MichalVarsanyi/VoxLink/Firmware/Vivado/Projects/VoxLink_Controller/VoxLink_Controller.runs/fifo_generator_0_synth_1/.vivado.begin.rst

<?xml version="1.0"?>
<ProcessHandle Version="1" Minor="0">
    <Process Command="vivado.bat" Owner="varsa" Host="LAPTOP-GK6ER3TV" Pid="4304" HostCore="22" HostMemory="033736019968">
    </Process>
</ProcessHandle>
