MichalVarsanyi/VoxLink/Hardware/Controller_Board/images/fb_res1.png

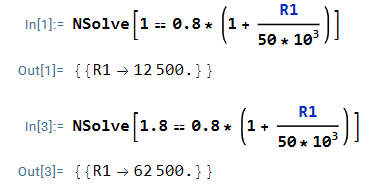
Hardware/Controller_Board/images/fb_res1.png
