MichalVarsanyi/VoxLink/Hardware/Controller_Board/images/hub_cfg.png

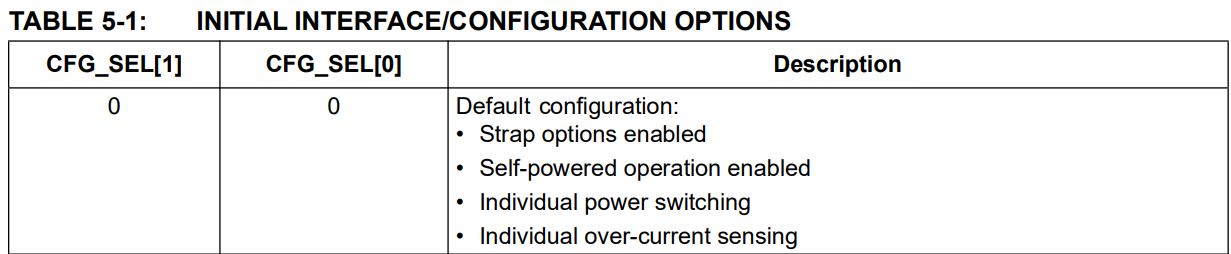
Hardware/Controller_Board/images/hub_cfg.png
