MichalVarsanyi/VoxLink/Hardware/Controller_Board/images/power_estimation.png

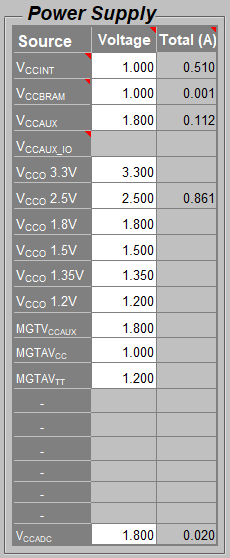
Hardware/Controller_Board/images/power_estimation.png
