MichalVarsanyi/VoxLink/Hardware/Programmer_Shell_Module/images/scheme_vox.png

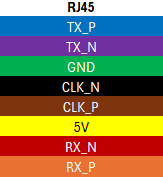
Hardware/Programmer_Shell_Module/images/scheme_vox.png
