MichalVarsanyi/VoxLink/Hardware/Sensor_Board/images/banana.bmp

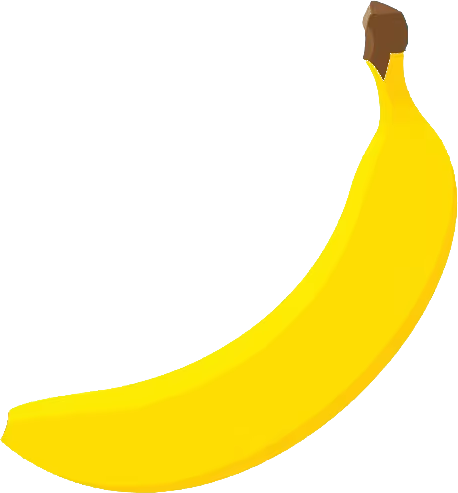
Hardware/Sensor_Board/images/banana.bmp
