MichalVarsanyi/VoxLink/Hardware/Sensor_Board/images/banana_flipped.bmp

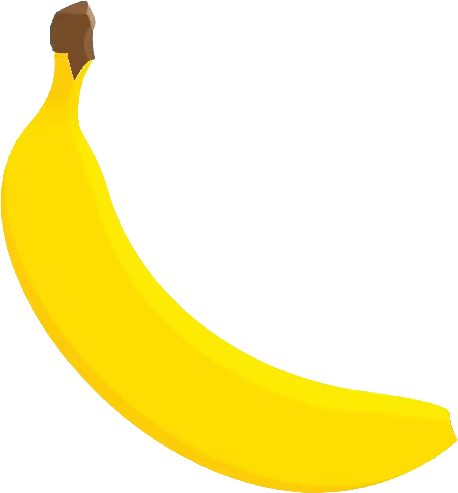
Hardware/Sensor_Board/images/banana_flipped.bmp
