MichalVarsanyi/VoxLink/Hardware/Sensor_Board/images/bno086_ps01.png

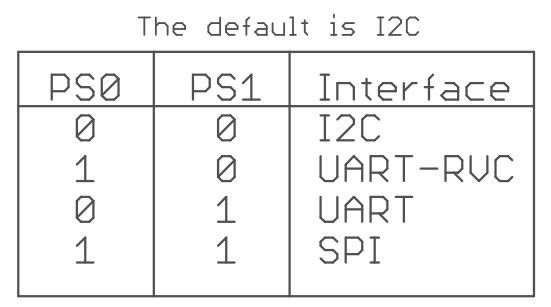
Hardware/Sensor_Board/images/bno086_ps01.png
