MichalVarsanyi/VoxLink/Hardware/Sensor_Board/images/datasheet_filtering.png

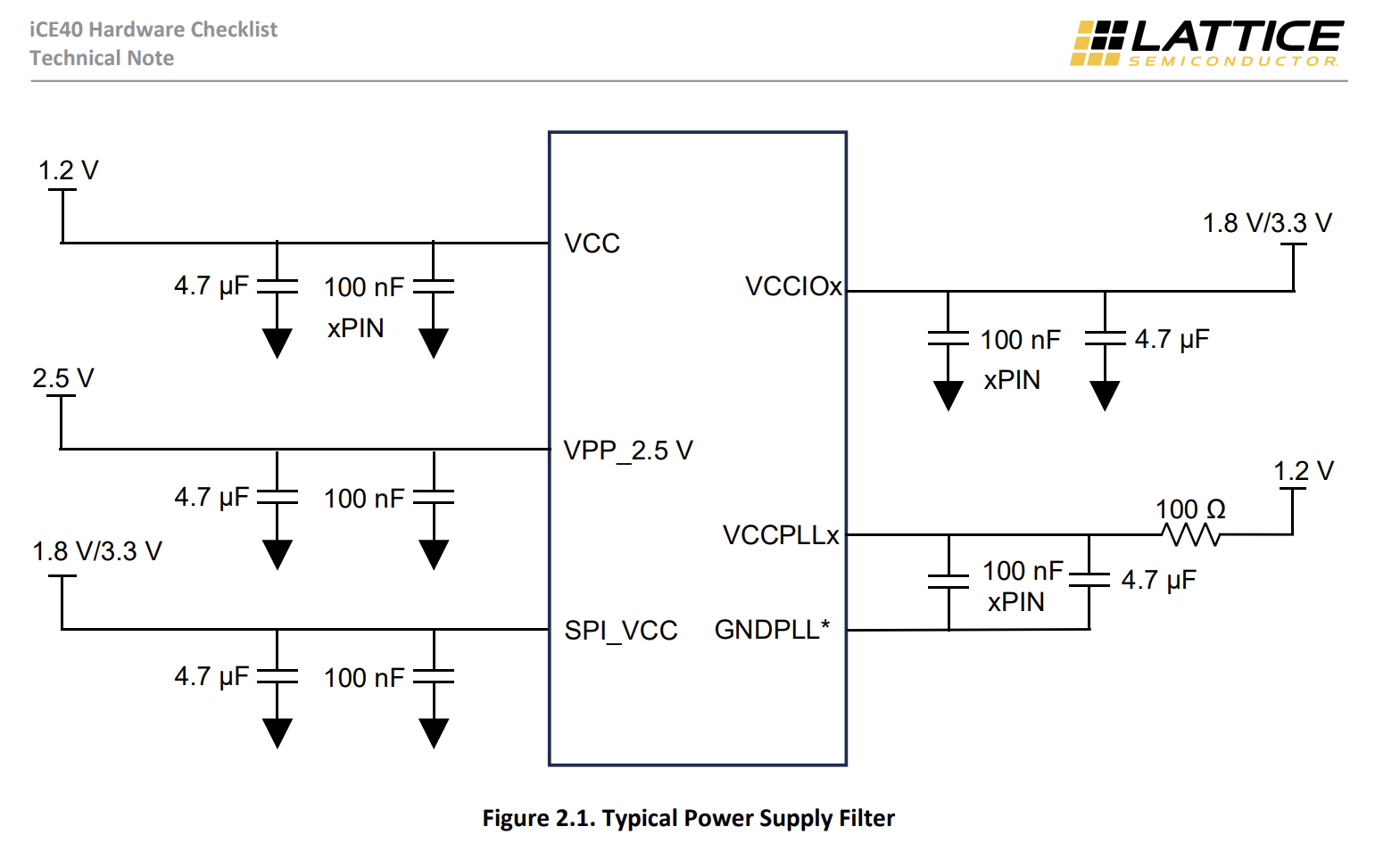
Hardware/Sensor_Board/images/datasheet_filtering.png
