MichalVarsanyi/VoxLink/Hardware/Sensor_Board/images/ilim.png

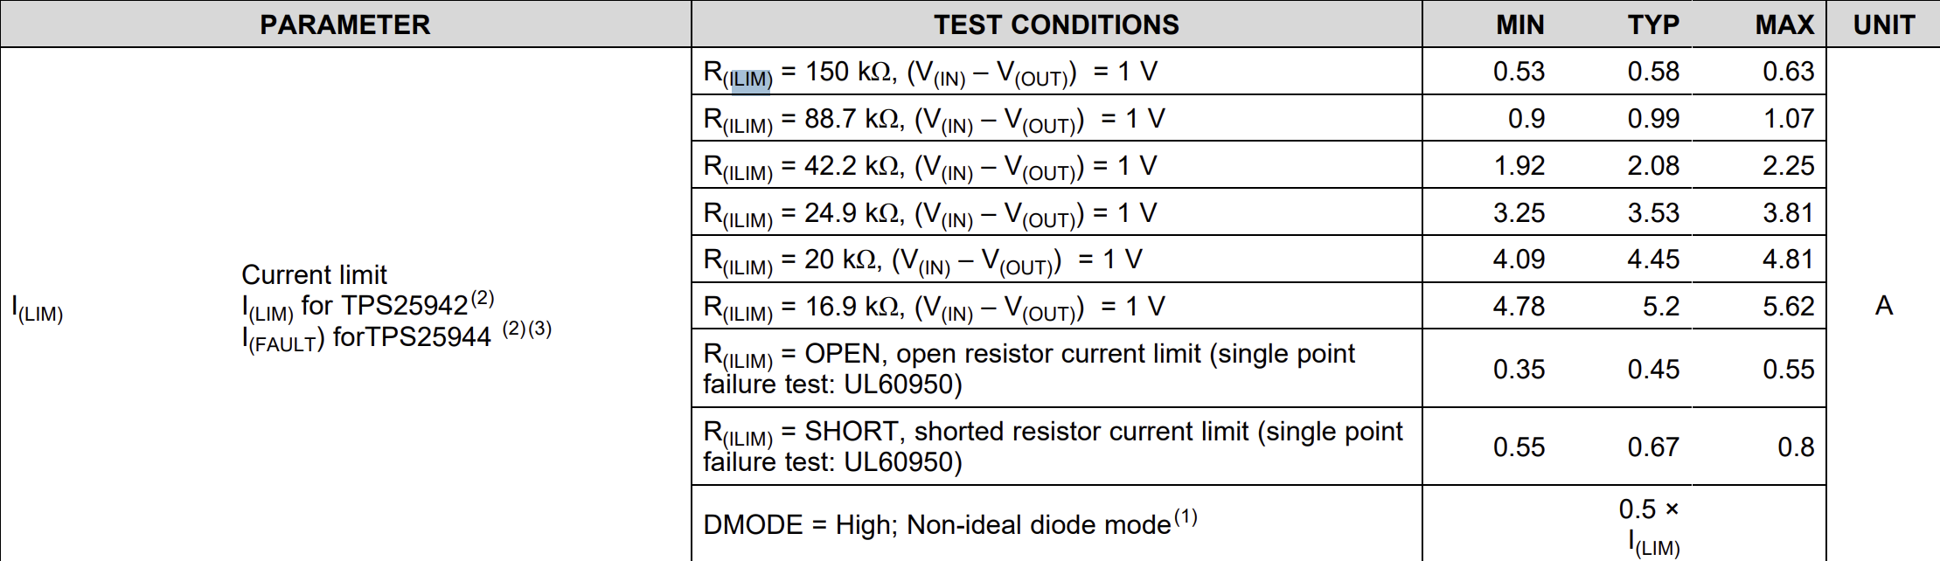
Hardware/Sensor_Board/images/ilim.png
