MichalVarsanyi/VoxLink/images/VoxLink_Block_Diagram_Simplified_Ethernet.jpg

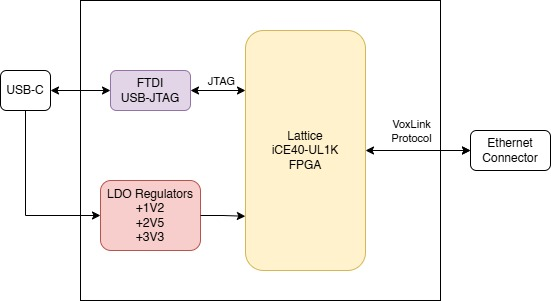
images/VoxLink_Block_Diagram_Simplified_Ethernet.jpg
