MichalVarsanyi/VoxLink/Hardware/Sensor_Board/images/ethernet_wiring.jpg

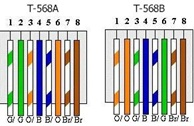
Hardware/Sensor_Board/images/ethernet_wiring.jpg
