MichalVarsanyi/VoxLink/Firmware/Lattice/Source/Verilog/Top_VoxLink_Protocol.v

//////////////////////////////////////////////////////////////////////////////////
// Company: Czech Technical University in Prague
// Engineer: Michal Varsanyi
// 
// Create Date: 26/DEC/2025
// Design Name: Top_VoxLink_Protocol
// Module Name: Top
// Project Name: VoxLink_Protocol
// Target Devices: VoxLink Sensor Board - iCE40UL1K-CM36AI
// Tool Versions: 
// Description: 
// 
// Dependencies: 
// 
// Revision: 1.0
// Revision 0.01 - File Created
// Additional Comments:
// 
//////////////////////////////////////////////////////////////////////////////////

module Top(
    // Clock
    input       clk_12mhz, 

    // Sensor
    inout       i2c_scl,
    inout       i2c_sda,
    output      bno_rstn,
    input       bno_interrupt,

    // LEDs
    output      led_io,

    // VoxLink
    input       vox_in_clk_p,
    input       vox_in_clk_n,

    output      vox_out_clk_p,
    output      vox_out_clk_n,

    input       vox_in_rxd_p,
    input       vox_in_rxd_n,

    output      vox_out_rxd_p,
    output      vox_out_rxd_n
);

//--------------------------------------------------------------------------------------------- //       
//  Wire Declarations
//--------------------------------------------------------------------------------------------- //

    localparam SYSTEM_CLOCK     = 84_000_000;
    localparam VOX_FREQUENCY    = 21_000_000;
    localparam I2C_FREQUENCY    = 400_000;

    // Clock and Reset
    wire            sys_clk;        // 100.5 MHz
    wire            sys_clkout;
    wire            sys_rst;
    wire            locked;
    assign          sys_rst = !locked;

    // VoxLink CDC outputs
    wire            vox_clk_sync;
    wire            vox_rxd_sync;

    // LED
    reg             led_io_r;
    reg             nack_sticky_r;


    //----------------EMI Improvements----------------//
    // Connect the _N to GND to facilitate low impedance return path
    assign vox_in_clk_n     = 1'b0;
    assign vox_out_clk_n    = 1'b0;
    assign vox_in_rxd_n     = 1'b0;
    assign vox_out_rxd_n    = 1'b0;

    // Assign the BNO RSTN pin to a deterministic value
    assign bno_rstn         = ~sys_rst;


//--------------------------------------------------------------------------------------------- //       
//  Clock
//--------------------------------------------------------------------------------------------- //

    // BUFG rounting of external clock
    wire clk_12mhz_bufg;

    // Routing inside the GBUF clock fabric
    SB_GB clk_in (
        .USER_SIGNAL_TO_GLOBAL_BUFFER(clk_12mhz),
        .GLOBAL_BUFFER_OUTPUT(clk_12mhz_bufg)
    );

    SB_PLL40_CORE #(
        .FEEDBACK_PATH("SIMPLE"),
        .DIVR(0),
        .DIVF(55),                  // VCO = 12 * 56 = 672 MHz
        .DIVQ(3),                   // F_out = 672 / 8 = 84 MHz
        .FILTER_RANGE(1)
    ) u_pll (
        .REFERENCECLK(clk_12mhz_bufg),
        .PLLOUTCORE(sys_clkout),
        .LOCK(locked),
        .EXTFEEDBACK(),
        .DYNAMICDELAY(),
        .RESETB(1'b1),              // Keep PLL enabled
        .BYPASS(1'b0)               // No bypass
    );

    SB_GB clk_pll (
        .USER_SIGNAL_TO_GLOBAL_BUFFER(sys_clkout),
        .GLOBAL_BUFFER_OUTPUT(sys_clk)
    );

//--------------------------------------------------------------------------------------------- //       
//  Cross Domain Crossing
//--------------------------------------------------------------------------------------------- //

    // VoxLink CLK Input
    wire vox_clk_ff1;
    wire vox_clk_ff2;

    SB_DFF vox_clk_cdc_stage_1 (
        .Q(vox_clk_ff1),
        .C(sys_clk),
        .D(vox_in_clk_p)
    );

    SB_DFF vox_clk_cdc_stage_2 (
        .Q(vox_clk_ff2),
        .C(sys_clk),
        .D(vox_clk_ff1)
    );

    assign vox_clk_sync = vox_clk_ff2;



    // VoxLink RXD Input
    wire vox_rxd_ff1;
    wire vox_rxd_ff2;

    SB_DFF vox_rxd_cdc_stage_1 (
        .Q(vox_rxd_ff1),
        .C(sys_clk),
        .D(vox_in_rxd_p)
    );

    SB_DFF vox_rxd_cdc_stage_2 (
        .Q(vox_rxd_ff2),
        .C(sys_clk),
        .D(vox_rxd_ff1)
    );

    assign vox_rxd_sync = vox_rxd_ff2;



    // Sensor Interrupt
    wire bno_interrupt_ff1;
    wire bno_interrupt_ff2;

    SB_DFF bno_interrupt_cdc_stage_1 (
        .Q(bno_interrupt_ff1),
        .C(sys_clk),
        .D(bno_interrupt)
    );

    SB_DFF bno_interrupt_cdc_stage_2 (
        .Q(bno_interrupt_ff2),
        .C(sys_clk),
        .D(bno_interrupt_ff1)
    );

    assign bno_interrupt_sync = bno_interrupt_ff2;


//--------------------------------------------------------------------------------------------- //
// VoxLink Multinode Protocol
//--------------------------------------------------------------------------------------------- //

    wire [9:0]      node_addr_r;
    wire            fifo_overflow_sticky;

    VoxLink_Multinode_Protocol #(
        .CLK_FREQ(SYSTEM_CLOCK),
        .VOX_FREQ(VOX_FREQUENCY)
    ) VoxLink_Multinode_Protocol_Inst (
        // General
        .sys_clk        (sys_clk),
        .sys_rst        (sys_rst),

        // Data
        .vox_transmit_packet(packet_data_latched),

        // VoxLink
        .vox_in_clk_p   (vox_clk_sync),
        .vox_in_rxd_p   (vox_rxd_sync),

        .vox_out_rxd_p  (vox_out_rxd_p),
        .vox_out_clk_p  (vox_out_clk_p),

        // Node
        .node_addr_r(node_addr_r),

        // Diagnostics
        .fifo_overflow_sticky(fifo_overflow_sticky)
    );

//--------------------------------------------------------------------------------------------- //
//  NACK Sticky Flag
//--------------------------------------------------------------------------------------------- //

    always @(posedge sys_clk or posedge sys_rst)
    begin
        if (sys_rst)
            nack_sticky_r <= 1'b0;
        else if (target_nack)
            nack_sticky_r <= 1'b1;
    end

//--------------------------------------------------------------------------------------------- //
//  RGB Infrastructure
//--------------------------------------------------------------------------------------------- //

    SB_RGBA_DRV #(
        .CURRENT_MODE("0b1"),
        .RGB0_CURRENT("0b000001"),
        .RGB1_CURRENT(),
        .RGB2_CURRENT()
    ) led_driver (
        .CURREN(1'b1),
        .RGBLEDEN(1'b1),

        .RGB0PWM(nack_sticky_r),
        .RGB1PWM(),
        .RGB2PWM(),

        .RGB0(led_io),
        .RGB1(),
        .RGB2()
    );

//--------------------------------------------------------------------------------------------- // 
// Blinky LED
//--------------------------------------------------------------------------------------------- // 

    // reg [26:0]  blink_counter;

    // always @(posedge sys_clk or posedge sys_rst)
    // begin
    //     if(sys_rst)
    //     begin
    //         led_io_r        <= 1'b1;
    //     end
    //     else
    //     begin
    //         if(blink_counter == {27{1'b1}})
    //         begin
    //             blink_counter   <= {27{1'b0}};
    //             led_io_r        <= ~led_io_r;
    //         end
    //         else
    //         begin
    //             blink_counter   <= blink_counter + 1;
    //         end
    //     end
    // end


//--------------------------------------------------------------------------------------------- // 
// I2C Driver
//--------------------------------------------------------------------------------------------- // 

    wire [7:0] tx_data;
    wire       trigger_tx;
    wire       tx_done;
    wire       target_nack;

    wire [7:0] rx_data;
    wire       trigger_rx;
    wire       rx_valid;

    wire       finish_transaction;
    wire       driver_waiting;
    wire       driver_finished_tranaction;

    VoxLink_I2C_Driver #(
        .CLK_FREQ(SYSTEM_CLOCK),  // System Clock Frequency
        .I2C_FREQ(I2C_FREQUENCY)        // Target I2C Speed
    ) VoxLink_I2C_Driver_inst (
        // General
        .sys_clk        (sys_clk),
        .sys_rst        (sys_rst),

        // I2C Interface
        .i2c_scl        (i2c_scl),
        .i2c_sda        (i2c_sda),

        // Control Signals
        .tx_data(tx_data),                          // Data to send
        .trigger_tx(trigger_tx),                    // Pulse HIGH to write the tx_data byte
        .tx_done(tx_done),                          // Pulses HIGH when writing the byte is complete
        .target_nack(target_nack),                  // HIGH = The sensor ignored us! (Did not ACK our write) Blasphemy!

        .rx_data(rx_data),                          // Data received
        .trigger_rx(trigger_rx),                    // Pulse HIGH to trigger a read operation
        .rx_valid(rx_valid),                        // Pulses HIGH when rx_data is valid

        .finish_transaction(finish_transaction),    // Set HIGH before the ACK of the last byte we want to receive + signal triggers the STOP sequence
        .driver_waiting(driver_waiting),            // Driver is waiting for command
        .driver_finished_tranaction(driver_finished_tranaction)     // Driver has finished a sequence of transaction commands and is now in the idle state
    );

//--------------------------------------------------------------------------------------------- // 
// BNO086 Sensor Driver
//--------------------------------------------------------------------------------------------- // 

    wire [79:0] sensor_data;
    wire        sensor_data_ready;

    VoxLink_BNO_Driver #(
        .BNO_ADDRESS(7'h4B)                         // Check the SA0 pin of the BNO086 in the schematic diagram
    ) VoxLink_BNO_Driver_Inst (
        // General
        .sys_clk(sys_clk),
        .sys_rst(sys_rst),
        
        // Control Signals
        .tx_data(tx_data),                          // Data to send
        .trigger_tx(trigger_tx),                    // Pulse HIGH to write the tx_data byte
        .tx_done(tx_done),                          // Pulses HIGH when writing the byte is complete
        .target_nack(target_nack),                  // HIGH = The sensor ignored us! (Did not ACK our write) Blasphemy!

        .rx_data(rx_data),                          // Data received
        .trigger_rx(trigger_rx),                    // Pulse HIGH to trigger a read operation
        .rx_valid(rx_valid),                        // Pulses HIGH when rx_data is valid

        .finish_transaction(finish_transaction),    // Set HIGH before the ACK of the last byte we want to receive + signal triggers the STOP sequence
        .driver_waiting(driver_waiting),            // Driver is waiting for command
        .driver_finished_tranaction(driver_finished_tranaction),    // Driver has finished a sequence of transaction commands and is now in the idle state

        // Sensor
        .bno_interrupt(bno_interrupt_sync),              // Interrupt from the BNO sensor

        .sensor_data(sensor_data),                  // Latched data from the sensor
        .sensor_data_ready(sensor_data_ready)
    );

//--------------------------------------------------------------------------------------------- // 
// VoxLink Packet Builder
//--------------------------------------------------------------------------------------------- // 

    wire [111:0] packet_data;
    wire         packet_ready;

    reg [111:0] packet_data_latched;

    assign vox_transmit_packet = packet_data_latched;

    always @(posedge sys_clk or posedge sys_rst)
    begin
        if (sys_rst)
        begin
            packet_data_latched <= 112'd0;
        end
        else if (packet_ready && node_addr_r != 10'd0)
        begin
            packet_data_latched <= packet_data;
        end
    end

    VoxLink_Packet_Builder #(
        .COMMAND(6'h03),
        .CLK_FREQ_HZ(SYSTEM_CLOCK)
    ) VoxLink_Packet_Builder_Inst (
        // General
        .sys_clk(sys_clk),
        .sys_rst(sys_rst),

        // Sensor Data
        .sensor_data(sensor_data),
        .sensor_data_ready(sensor_data_ready),

        // Node Info
        .address(node_addr_r),

        // Output Packet
        .packet_data(packet_data),
        .packet_ready(packet_ready)
    );
endmodule
