MichalVarsanyi/VoxLink/Firmware/Vivado/Projects/VoxLink_Controller/VoxLink_Controller.srcs/sources_1/new/VoxLink_BRAM_Storage.v

`timescale 1ns / 1ps

module VoxLink_BRAM_Storage (
    input           sys_clk,

    input  [111:0]  rx_packet,
    input           rx_valid,

    input  [6:0]    node_select,
    output [111:0]  node_packet
);

    wire [6:0]      bram_addr = rx_valid ? rx_packet[108:102] : node_select;
    wire [111:0]    bram_dout;

    blk_mem_gen_0 u_bram (
        .clka  (sys_clk),
        .ena   (1'b1),
        .wea   (rx_valid),
        .addra (bram_addr),
        .dina  (rx_packet),
        .douta (bram_dout)
    );

    assign node_packet = bram_dout;

endmodule
