MichalVarsanyi/VoxLink/Firmware/Vivado/Projects/VoxLink_Controller/VoxLink_Controller.cache/ip/2024.1/a/6/a6a7915305ae47ab/blk_mem_gen_0_stub.v

// Copyright 1986-2022 Xilinx, Inc. All Rights Reserved.
// Copyright 2022-2024 Advanced Micro Devices, Inc. All Rights Reserved.
// --------------------------------------------------------------------------------
// Tool Version: Vivado v.2024.1 (win64) Build 5076996 Wed May 22 18:37:14 MDT 2024
// Date        : Tue May  5 16:36:00 2026
// Host        : LAPTOP-GK6ER3TV running 64-bit major release  (build 9200)
// Command     : write_verilog -force -mode synth_stub -rename_top decalper_eb_ot_sdeen_pot_pi_dehcac_xnilix -prefix
//               decalper_eb_ot_sdeen_pot_pi_dehcac_xnilix_ blk_mem_gen_0_stub.v
// Design      : blk_mem_gen_0
// Purpose     : Stub declaration of top-level module interface
// Device      : xc7a35tcsg324-1
// --------------------------------------------------------------------------------

// This empty module with port declaration file causes synthesis tools to infer a black box for IP.
// The synthesis directives are for Synopsys Synplify support to prevent IO buffer insertion.
// Please paste the declaration into a Verilog source file or add the file as an additional source.
(* x_core_info = "blk_mem_gen_v8_4_8,Vivado 2024.1" *)
module decalper_eb_ot_sdeen_pot_pi_dehcac_xnilix(clka, ena, wea, addra, dina, douta)
/* synthesis syn_black_box black_box_pad_pin="ena,wea[0:0],addra[6:0],dina[111:0],douta[111:0]" */
/* synthesis syn_force_seq_prim="clka" */;
  input clka /* synthesis syn_isclock = 1 */;
  input ena;
  input [0:0]wea;
  input [6:0]addra;
  input [111:0]dina;
  output [111:0]douta;
endmodule
