MichalVarsanyi/VoxLink/Firmware/Vivado/Projects/VoxLink_Controller/VoxLink_Controller.cache/ip/2024.1/6/f/6fbaab5b1b3133b9/u_ila_0_stub.v

// Copyright 1986-2022 Xilinx, Inc. All Rights Reserved.
// Copyright 2022-2024 Advanced Micro Devices, Inc. All Rights Reserved.
// --------------------------------------------------------------------------------
// Tool Version: Vivado v.2024.1 (win64) Build 5076996 Wed May 22 18:37:14 MDT 2024
// Date        : Thu Apr 30 17:34:39 2026
// Host        : LAPTOP-GK6ER3TV running 64-bit major release  (build 9200)
// Command     : write_verilog -force -mode synth_stub -rename_top decalper_eb_ot_sdeen_pot_pi_dehcac_xnilix -prefix
//               decalper_eb_ot_sdeen_pot_pi_dehcac_xnilix_ u_ila_0_stub.v
// Design      : u_ila_0
// Purpose     : Stub declaration of top-level module interface
// Device      : xc7a35tcsg324-1
// --------------------------------------------------------------------------------

// This empty module with port declaration file causes synthesis tools to infer a black box for IP.
// The synthesis directives are for Synopsys Synplify support to prevent IO buffer insertion.
// Please paste the declaration into a Verilog source file or add the file as an additional source.
(* X_CORE_INFO = "ila,Vivado 2024.1" *)
module decalper_eb_ot_sdeen_pot_pi_dehcac_xnilix(clk, probe0, probe1, probe2, probe3, probe4, probe5, 
  probe6, probe7, probe8, probe9, probe10, probe11, probe12, probe13)
/* synthesis syn_black_box black_box_pad_pin="probe0[13:0],probe1[2:0],probe2[14:0],probe3[7:0],probe4[31:0],probe5[14:0],probe6[39:0],probe7[1:0],probe8[111:0],probe9[14:0],probe10[7:0],probe11[63:0],probe12[0:0],probe13[0:0]" */
/* synthesis syn_force_seq_prim="clk" */;
  input clk /* synthesis syn_isclock = 1 */;
  input [13:0]probe0;
  input [2:0]probe1;
  input [14:0]probe2;
  input [7:0]probe3;
  input [31:0]probe4;
  input [14:0]probe5;
  input [39:0]probe6;
  input [1:0]probe7;
  input [111:0]probe8;
  input [14:0]probe9;
  input [7:0]probe10;
  input [63:0]probe11;
  input [0:0]probe12;
  input [0:0]probe13;
endmodule
