MichalVarsanyi/VoxLink/Firmware/Vivado/Projects/VoxLink_Controller/VoxLink_Controller.cache/ip/2024.1/6/f/6fbaab5b1b3133b9/u_ila_0_stub.vhdl

-- Copyright 1986-2022 Xilinx, Inc. All Rights Reserved.
-- Copyright 2022-2024 Advanced Micro Devices, Inc. All Rights Reserved.
-- --------------------------------------------------------------------------------
-- Tool Version: Vivado v.2024.1 (win64) Build 5076996 Wed May 22 18:37:14 MDT 2024
-- Date        : Thu Apr 30 17:34:39 2026
-- Host        : LAPTOP-GK6ER3TV running 64-bit major release  (build 9200)
-- Command     : write_vhdl -force -mode synth_stub -rename_top decalper_eb_ot_sdeen_pot_pi_dehcac_xnilix -prefix
--               decalper_eb_ot_sdeen_pot_pi_dehcac_xnilix_ u_ila_0_stub.vhdl
-- Design      : u_ila_0
-- Purpose     : Stub declaration of top-level module interface
-- Device      : xc7a35tcsg324-1
-- --------------------------------------------------------------------------------
library IEEE;
use IEEE.STD_LOGIC_1164.ALL;

entity decalper_eb_ot_sdeen_pot_pi_dehcac_xnilix is
  Port ( 
    clk : in STD_LOGIC;
    probe0 : in STD_LOGIC_VECTOR ( 13 downto 0 );
    probe1 : in STD_LOGIC_VECTOR ( 2 downto 0 );
    probe2 : in STD_LOGIC_VECTOR ( 14 downto 0 );
    probe3 : in STD_LOGIC_VECTOR ( 7 downto 0 );
    probe4 : in STD_LOGIC_VECTOR ( 31 downto 0 );
    probe5 : in STD_LOGIC_VECTOR ( 14 downto 0 );
    probe6 : in STD_LOGIC_VECTOR ( 39 downto 0 );
    probe7 : in STD_LOGIC_VECTOR ( 1 downto 0 );
    probe8 : in STD_LOGIC_VECTOR ( 111 downto 0 );
    probe9 : in STD_LOGIC_VECTOR ( 14 downto 0 );
    probe10 : in STD_LOGIC_VECTOR ( 7 downto 0 );
    probe11 : in STD_LOGIC_VECTOR ( 63 downto 0 );
    probe12 : in STD_LOGIC_VECTOR ( 0 to 0 );
    probe13 : in STD_LOGIC_VECTOR ( 0 to 0 )
  );

end decalper_eb_ot_sdeen_pot_pi_dehcac_xnilix;

architecture stub of decalper_eb_ot_sdeen_pot_pi_dehcac_xnilix is
attribute syn_black_box : boolean;
attribute black_box_pad_pin : string;
attribute syn_black_box of stub : architecture is true;
attribute black_box_pad_pin of stub : architecture is "clk,probe0[13:0],probe1[2:0],probe2[14:0],probe3[7:0],probe4[31:0],probe5[14:0],probe6[39:0],probe7[1:0],probe8[111:0],probe9[14:0],probe10[7:0],probe11[63:0],probe12[0:0],probe13[0:0]";
attribute X_CORE_INFO : string;
attribute X_CORE_INFO of stub : architecture is "ila,Vivado 2024.1";
begin
end;
