MichalVarsanyi/VoxLink/Firmware/Vivado/Projects/VoxLink_Controller/VoxLink_Controller.ip_user_files/ip/fifo_generator_0/fifo_generator_0_stub.vhdl

-- Copyright 1986-2022 Xilinx, Inc. All Rights Reserved.
-- Copyright 2022-2024 Advanced Micro Devices, Inc. All Rights Reserved.
-- --------------------------------------------------------------------------------
-- Tool Version: Vivado v.2024.1 (win64) Build 5076996 Wed May 22 18:37:14 MDT 2024
-- Date        : Mon Apr 27 17:44:07 2026
-- Host        : LAPTOP-GK6ER3TV running 64-bit major release  (build 9200)
-- Command     : write_vhdl -force -mode synth_stub
--               c:/Users/varsa/Desktop/School/5_semester/BachelorProject/VoxLink/Firmware/Vivado/Projects/VoxLink_Controller/MV_test.gen/sources_1/ip/fifo_generator_0/fifo_generator_0_stub.vhdl
-- Design      : fifo_generator_0
-- Purpose     : Stub declaration of top-level module interface
-- Device      : xc7a35tcsg324-1
-- --------------------------------------------------------------------------------
library IEEE;
use IEEE.STD_LOGIC_1164.ALL;

entity fifo_generator_0 is
  Port ( 
    clk : in STD_LOGIC;
    srst : in STD_LOGIC;
    din : in STD_LOGIC_VECTOR ( 7 downto 0 );
    wr_en : in STD_LOGIC;
    rd_en : in STD_LOGIC;
    dout : out STD_LOGIC_VECTOR ( 7 downto 0 );
    full : out STD_LOGIC;
    empty : out STD_LOGIC;
    valid : out STD_LOGIC;
    data_count : out STD_LOGIC_VECTOR ( 10 downto 0 )
  );

end fifo_generator_0;

architecture stub of fifo_generator_0 is
attribute syn_black_box : boolean;
attribute black_box_pad_pin : string;
attribute syn_black_box of stub : architecture is true;
attribute black_box_pad_pin of stub : architecture is "clk,srst,din[7:0],wr_en,rd_en,dout[7:0],full,empty,valid,data_count[10:0]";
attribute x_core_info : string;
attribute x_core_info of stub : architecture is "fifo_generator_v13_2_10,Vivado 2024.1";
begin
end;
