MichalVarsanyi/VoxLink/Firmware/Lattice/Projects/TinyFPGA_BringUp/sources/TFPGA_PLL_inst.v

TFPGA_PLL TFPGA_PLL_inst(.REFERENCECLK(),
                         .PLLOUTCORE(),
                         .PLLOUTGLOBAL(),
                         .DYNAMICDELAY(),
                         .RESET(),
                         .LOCK());
