MichalVarsanyi/VoxLink/Firmware/Lattice/Projects/Core_Module_BringUp/Core_Module_BringUp_Implmnt/sbt/outputs/simulation_netlist/Top_sbt.v

// ******************************************************************************

// iCEcube Netlister

// Version:            2020.12.27943

// Build Date:         Dec  9 2020 18:18:12

// File Generated:     Apr 23 2026 17:54:58

// Purpose:            Post-Route Verilog/VHDL netlist for timing simulation

// Copyright (C) 2006-2010 by Lattice Semiconductor Corp. All rights reserved.

// ******************************************************************************

// Verilog file for cell "Top" view "INTERFACE"

module Top (
    led_io,
    clk_12mhz);

    output led_io;
    input clk_12mhz;

    wire N__1301;
    wire N__1300;
    wire N__1299;
    wire N__1282;
    wire N__1281;
    wire N__1278;
    wire N__1275;
    wire N__1270;
    wire N__1269;
    wire N__1266;
    wire N__1263;
    wire N__1258;
    wire N__1255;
    wire N__1254;
    wire N__1251;
    wire N__1248;
    wire N__1243;
    wire N__1242;
    wire N__1239;
    wire N__1236;
    wire N__1231;
    wire N__1228;
    wire N__1225;
    wire N__1224;
    wire N__1221;
    wire N__1218;
    wire N__1213;
    wire N__1212;
    wire N__1209;
    wire N__1206;
    wire N__1201;
    wire N__1198;
    wire N__1197;
    wire N__1194;
    wire N__1191;
    wire N__1186;
    wire N__1185;
    wire N__1182;
    wire N__1179;
    wire N__1174;
    wire N__1171;
    wire N__1168;
    wire N__1167;
    wire N__1164;
    wire N__1161;
    wire N__1156;
    wire N__1155;
    wire N__1152;
    wire N__1149;
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
    wire bfn_5_10_0_;
    wire blink_counter_cry_24;
    wire blink_counter_cry_25;
    wire clk_12mhz_bufg;
    wire GB_BUFFER_clk_12mhz_bufg_THRU_CO;
    wire blink_counter11_24_cascade_;
    wire led_io_rZ0;
    wire sys_clk;
    wire blink_counterZ0Z_3;
    wire blink_counterZ0Z_2;
    wire blink_counterZ0Z_4;
    wire blink_counterZ0Z_5;
    wire blink_counterZ0Z_23;
    wire blink_counterZ0Z_1;
    wire blink_counter11_14_cascade_;
    wire blink_counterZ0Z_0;
    wire blink_counter11_20;
    wire blink_counterZ0Z_21;
    wire blink_counterZ0Z_20;
    wire blink_counterZ0Z_19;
    wire blink_counterZ0Z_22;
    wire blink_counter11_19;
    wire blink_counterZ0Z_11;
    wire blink_counterZ0Z_10;
    wire blink_counterZ0Z_12;
    wire blink_counterZ0Z_13;
    wire blink_counter11_16;
    wire blink_counterZ0Z_17;
    wire blink_counterZ0Z_16;
    wire blink_counterZ0Z_26;
    wire blink_counterZ0Z_18;
    wire blink_counter11_18;
    wire blink_counterZ0Z_7;
    wire blink_counterZ0Z_6;
    wire blink_counterZ0Z_9;
    wire blink_counterZ0Z_8;
    wire blink_counter11_15;
    wire blink_counterZ0Z_15;
    wire blink_counterZ0Z_14;
    wire blink_counterZ0Z_24;
    wire blink_counterZ0Z_25;
    wire blink_counter11_17;
    wire CONSTANT_ONE_NET;
    wire locked_g;
    wire locked_i;
    wire _gnd_net_;

    defparam u_pll.DELAY_ADJUSTMENT_MODE_FEEDBACK="FIXED";
    defparam u_pll.TEST_MODE=1'b0;
    defparam u_pll.SHIFTREG_DIV_MODE=2'b00;
    defparam u_pll.PLLOUT_SELECT="GENCLK";
    defparam u_pll.FILTER_RANGE=3'b001;
    defparam u_pll.FEEDBACK_PATH="SIMPLE";
    defparam u_pll.FDA_RELATIVE=4'b0000;
    defparam u_pll.FDA_FEEDBACK=4'b0000;
    defparam u_pll.ENABLE_ICEGATE=1'b0;
    defparam u_pll.DIVR=4'b0000;
    defparam u_pll.DIVQ=3'b011;
    defparam u_pll.DIVF=7'b1000010;
    defparam u_pll.DELAY_ADJUSTMENT_MODE_RELATIVE="FIXED";
    SB_PLL40_CORE u_pll (
            .EXTFEEDBACK(),
            .LATCHINPUTVALUE(),
            .SCLK(),
            .SDO(),
            .LOCK(PLL_BUFFER_u_pll_LOCK_THRU_CO),
            .PLLOUTCORE(sys_clkout),
            .REFERENCECLK(N__874),
            .RESETB(N__968),
            .BYPASS(GNDG0),
            .SDI(),
            .DYNAMICDELAY({GNDG0,GNDG0,GNDG0,GNDG0,GNDG0,GNDG0,GNDG0,GNDG0}),
            .PLLOUTGLOBAL());
    IO_PAD clk_12mhz_ibuf_iopad (
            .OE(N__1301),
            .DIN(N__1300),
            .DOUT(N__1299),
            .PACKAGEPIN(clk_12mhz));
    defparam clk_12mhz_ibuf_preio.NEG_TRIGGER=1'b0;
    defparam clk_12mhz_ibuf_preio.PIN_TYPE=6'b000001;
    PRE_IO clk_12mhz_ibuf_preio (
            .PADOEN(N__1301),
            .PADOUT(N__1300),
            .PADIN(N__1299),
            .CLOCKENABLE(),
            .DOUT1(),
            .OUTPUTENABLE(),
            .DIN0(clk_12mhz_c),
            .DOUT0(),
            .INPUTCLK(),
            .LATCHINPUTVALUE(),
            .DIN1(),
            .OUTPUTCLK());
    InMux I__288 (
            .O(N__1282),
            .I(N__1278));
    InMux I__287 (
            .O(N__1281),
            .I(N__1275));
    LocalMux I__286 (
            .O(N__1278),
            .I(blink_counterZ0Z_21));
    LocalMux I__285 (
            .O(N__1275),
            .I(blink_counterZ0Z_21));
    InMux I__284 (
            .O(N__1270),
            .I(N__1266));
    InMux I__283 (
            .O(N__1269),
            .I(N__1263));
    LocalMux I__282 (
            .O(N__1266),
            .I(blink_counterZ0Z_20));
    LocalMux I__281 (
            .O(N__1263),
            .I(blink_counterZ0Z_20));
    CascadeMux I__280 (
            .O(N__1258),
            .I(N__1255));
    InMux I__279 (
            .O(N__1255),
            .I(N__1251));
    InMux I__278 (
            .O(N__1254),
            .I(N__1248));
    LocalMux I__277 (
            .O(N__1251),
            .I(blink_counterZ0Z_19));
    LocalMux I__276 (
            .O(N__1248),
            .I(blink_counterZ0Z_19));
    InMux I__275 (
            .O(N__1243),
            .I(N__1239));
    InMux I__274 (
            .O(N__1242),
            .I(N__1236));
    LocalMux I__273 (
            .O(N__1239),
            .I(blink_counterZ0Z_22));
    LocalMux I__272 (
            .O(N__1236),
            .I(blink_counterZ0Z_22));
    InMux I__271 (
            .O(N__1231),
            .I(N__1228));
    LocalMux I__270 (
            .O(N__1228),
            .I(blink_counter11_19));
    InMux I__269 (
            .O(N__1225),
            .I(N__1221));
    InMux I__268 (
            .O(N__1224),
            .I(N__1218));
    LocalMux I__267 (
            .O(N__1221),
            .I(blink_counterZ0Z_11));
    LocalMux I__266 (
            .O(N__1218),
            .I(blink_counterZ0Z_11));
    InMux I__265 (
            .O(N__1213),
            .I(N__1209));
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
    ICE_CARRY_IN_MUX IN_MUX_bfv_5_8_0_ (
            .carryinitin(blink_counter_cry_7),
            .carryinitout(bfn_5_8_0_));
    defparam IN_MUX_bfv_5_9_0_.C_INIT=2'b10;
    ICE_CARRY_IN_MUX IN_MUX_bfv_5_9_0_ (
            .carryinitin(blink_counter_cry_15),
            .carryinitout(bfn_5_9_0_));
    defparam IN_MUX_bfv_5_10_0_.C_INIT=2'b10;
    ICE_CARRY_IN_MUX IN_MUX_bfv_5_10_0_ (
            .carryinitin(blink_counter_cry_23),
            .carryinitout(bfn_5_10_0_));
    GND GND (
            .Y(GNDG0));
    ICE_GB clk_in (
            .USERSIGNALTOGLOBALBUFFER(N__652),
            .GLOBALBUFFEROUTPUT(clk_12mhz_bufg));
    defparam led_driver.CURRENT_MODE="0b1";
    defparam led_driver.RGB2_CURRENT="0b000000";
    defparam led_driver.RGB1_CURRENT="0b000000";
    defparam led_driver.RGB0_CURRENT="0b000001";
    SB_RGBA_DRV led_driver (
            .RGBLEDEN(N__982),
            .RGB2PWM(),
            .RGB1(),
            .CURREN(N__981),
            .RGB2(),
            .RGB1PWM(),
            .RGB0PWM(N__856),
            .RGB0(led_io));
    ICE_GB u_pll_RNISDD6 (
            .USERSIGNALTOGLOBALBUFFER(N__607),
            .GLOBALBUFFEROUTPUT(locked_g));
    VCC VCC (
            .Y(VCCG0));
    ICE_GB clk_pll (
            .USERSIGNALTOGLOBALBUFFER(N__631),
            .GLOBALBUFFEROUTPUT(sys_clk));
    GND GND_Inst (
            .Y(_gnd_net_));
    defparam PLL_BUFFER_u_pll_LOCK_THRU_LUT4_0_LC_1_1_0.C_ON=1'b0;
    defparam PLL_BUFFER_u_pll_LOCK_THRU_LUT4_0_LC_1_1_0.SEQ_MODE=4'b0000;
    defparam PLL_BUFFER_u_pll_LOCK_THRU_LUT4_0_LC_1_1_0.LUT_INIT=16'b1111111100000000;
    LogicCell40 PLL_BUFFER_u_pll_LOCK_THRU_LUT4_0_LC_1_1_0 (
            .in0(_gnd_net_),
            .in1(_gnd_net_),
            .in2(_gnd_net_),
            .in3(N__613),
            .lcout(locked),
            .ltout(),
            .carryin(_gnd_net_),
            .carryout(),
            .clk(_gnd_net_),
            .ce(),
            .sr(_gnd_net_));
    defparam blink_counter_0_LC_5_7_0.C_ON=1'b1;
    defparam blink_counter_0_LC_5_7_0.SEQ_MODE=4'b1000;
    defparam blink_counter_0_LC_5_7_0.LUT_INIT=16'b1001100101100110;
    LogicCell40 blink_counter_0_LC_5_7_0 (
            .in0(_gnd_net_),
            .in1(N__723),
            .in2(_gnd_net_),
            .in3(N__592),
            .lcout(blink_counterZ0Z_0),
            .ltout(),
            .carryin(bfn_5_7_0_),
            .carryout(blink_counter_cry_0),
            .clk(N__828),
            .ce(N__930),
            .sr(_gnd_net_));
    defparam blink_counter_1_LC_5_7_1.C_ON=1'b1;
    defparam blink_counter_1_LC_5_7_1.SEQ_MODE=4'b1000;
    defparam blink_counter_1_LC_5_7_1.LUT_INIT=16'b1001100101100110;
    LogicCell40 blink_counter_1_LC_5_7_1 (
            .in0(_gnd_net_),
            .in1(N__738),
            .in2(_gnd_net_),
            .in3(N__589),
            .lcout(blink_counterZ0Z_1),
            .ltout(),
            .carryin(blink_counter_cry_0),
            .carryout(blink_counter_cry_1),
            .clk(N__828),
            .ce(N__930),
            .sr(_gnd_net_));
    defparam blink_counter_2_LC_5_7_2.C_ON=1'b1;
    defparam blink_counter_2_LC_5_7_2.SEQ_MODE=4'b1000;
    defparam blink_counter_2_LC_5_7_2.LUT_INIT=16'b1001100101100110;
    LogicCell40 blink_counter_2_LC_5_7_2 (
            .in0(_gnd_net_),
            .in1(N__795),
            .in2(_gnd_net_),
            .in3(N__586),
            .lcout(blink_counterZ0Z_2),
            .ltout(),
            .carryin(blink_counter_cry_1),
            .carryout(blink_counter_cry_2),
            .clk(N__828),
            .ce(N__930),
            .sr(_gnd_net_));
    defparam blink_counter_3_LC_5_7_3.C_ON=1'b1;
    defparam blink_counter_3_LC_5_7_3.SEQ_MODE=4'b1000;
    defparam blink_counter_3_LC_5_7_3.LUT_INIT=16'b1001100101100110;
    LogicCell40 blink_counter_3_LC_5_7_3 (
            .in0(_gnd_net_),
            .in1(N__807),
            .in2(_gnd_net_),
            .in3(N__583),
            .lcout(blink_counterZ0Z_3),
            .ltout(),
            .carryin(blink_counter_cry_2),
            .carryout(blink_counter_cry_3),
            .clk(N__828),
            .ce(N__930),
            .sr(_gnd_net_));
    defparam blink_counter_4_LC_5_7_4.C_ON=1'b1;
    defparam blink_counter_4_LC_5_7_4.SEQ_MODE=4'b1000;
    defparam blink_counter_4_LC_5_7_4.LUT_INIT=16'b1001100101100110;
    LogicCell40 blink_counter_4_LC_5_7_4 (
            .in0(_gnd_net_),
            .in1(N__777),
            .in2(_gnd_net_),
            .in3(N__580),
            .lcout(blink_counterZ0Z_4),
            .ltout(),
            .carryin(blink_counter_cry_3),
            .carryout(blink_counter_cry_4),
            .clk(N__828),
            .ce(N__930),
            .sr(_gnd_net_));
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
    defparam blink_counter_23_LC_5_9_7.SEQ_MODE=4'b1000;
    defparam blink_counter_23_LC_5_9_7.LUT_INIT=16'b1001100101100110;
    LogicCell40 blink_counter_23_LC_5_9_7 (
            .in0(_gnd_net_),
            .in1(N__750),
            .in2(_gnd_net_),
            .in3(N__682),
            .lcout(blink_counterZ0Z_23),
            .ltout(),
            .carryin(blink_counter_cry_22),
            .carryout(blink_counter_cry_23),
            .clk(N__826),
            .ce(N__935),
            .sr(_gnd_net_));
    defparam blink_counter_24_LC_5_10_0.C_ON=1'b1;
    defparam blink_counter_24_LC_5_10_0.SEQ_MODE=4'b1000;
    defparam blink_counter_24_LC_5_10_0.LUT_INIT=16'b1001100101100110;
    LogicCell40 blink_counter_24_LC_5_10_0 (
            .in0(_gnd_net_),
            .in1(N__1017),
            .in2(_gnd_net_),
            .in3(N__898),
            .lcout(blink_counterZ0Z_24),
            .ltout(),
            .carryin(bfn_5_10_0_),
            .carryout(blink_counter_cry_24),
            .clk(N__825),
            .ce(N__936),
            .sr(_gnd_net_));
    defparam blink_counter_25_LC_5_10_1.C_ON=1'b1;
    defparam blink_counter_25_LC_5_10_1.SEQ_MODE=4'b1000;
    defparam blink_counter_25_LC_5_10_1.LUT_INIT=16'b1001100101100110;
    LogicCell40 blink_counter_25_LC_5_10_1 (
            .in0(_gnd_net_),
            .in1(N__1003),
            .in2(_gnd_net_),
            .in3(N__895),
            .lcout(blink_counterZ0Z_25),
            .ltout(),
            .carryin(blink_counter_cry_24),
            .carryout(blink_counter_cry_25),
            .clk(N__825),
            .ce(N__936),
            .sr(_gnd_net_));
    defparam blink_counter_26_LC_5_10_2.C_ON=1'b0;
    defparam blink_counter_26_LC_5_10_2.SEQ_MODE=4'b1000;
    defparam blink_counter_26_LC_5_10_2.LUT_INIT=16'b0011001111001100;
    LogicCell40 blink_counter_26_LC_5_10_2 (
            .in0(_gnd_net_),
            .in1(N__1137),
            .in2(_gnd_net_),
            .in3(N__892),
            .lcout(blink_counterZ0Z_26),
            .ltout(),
            .carryin(_gnd_net_),
            .carryout(),
            .clk(N__825),
            .ce(N__936),
            .sr(_gnd_net_));
    defparam GB_BUFFER_clk_12mhz_bufg_THRU_LUT4_0_LC_6_1_2.C_ON=1'b0;
    defparam GB_BUFFER_clk_12mhz_bufg_THRU_LUT4_0_LC_6_1_2.SEQ_MODE=4'b0000;
    defparam GB_BUFFER_clk_12mhz_bufg_THRU_LUT4_0_LC_6_1_2.LUT_INIT=16'b1010101010101010;
    LogicCell40 GB_BUFFER_clk_12mhz_bufg_THRU_LUT4_0_LC_6_1_2 (
            .in0(N__889),
            .in1(_gnd_net_),
            .in2(_gnd_net_),
            .in3(_gnd_net_),
            .lcout(GB_BUFFER_clk_12mhz_bufg_THRU_CO),
            .ltout(),
            .carryin(_gnd_net_),
            .carryout(),
            .clk(_gnd_net_),
            .ce(),
            .sr(_gnd_net_));
    defparam led_io_r_RNO_3_LC_6_7_0.C_ON=1'b0;
    defparam led_io_r_RNO_3_LC_6_7_0.SEQ_MODE=4'b0000;
    defparam led_io_r_RNO_3_LC_6_7_0.LUT_INIT=16'b1000000000000000;
    LogicCell40 led_io_r_RNO_3_LC_6_7_0 (
            .in0(N__1111),
            .in1(N__991),
            .in2(N__1051),
            .in3(N__1174),
            .lcout(),
            .ltout(blink_counter11_24_cascade_),
            .carryin(_gnd_net_),
            .carryout(),
            .clk(_gnd_net_),
            .ce(),
            .sr(_gnd_net_));
    defparam led_io_r_LC_6_7_1.C_ON=1'b0;
    defparam led_io_r_LC_6_7_1.SEQ_MODE=4'b1011;
    defparam led_io_r_LC_6_7_1.LUT_INIT=16'b0110101010101010;
    LogicCell40 led_io_r_LC_6_7_1 (
            .in0(N__840),
            .in1(N__1231),
            .in2(N__859),
            .in3(N__712),
            .lcout(led_io_rZ0),
            .ltout(),
            .carryin(_gnd_net_),
            .carryout(),
            .clk(N__829),
            .ce(),
            .sr(N__913));
    defparam led_io_r_RNO_4_LC_6_7_3.C_ON=1'b0;
    defparam led_io_r_RNO_4_LC_6_7_3.SEQ_MODE=4'b0000;
    defparam led_io_r_RNO_4_LC_6_7_3.LUT_INIT=16'b1000000000000000;
    LogicCell40 led_io_r_RNO_4_LC_6_7_3 (
            .in0(N__808),
            .in1(N__796),
            .in2(N__784),
            .in3(N__765),
            .lcout(),
            .ltout(blink_counter11_14_cascade_),
            .carryin(_gnd_net_),
            .carryout(),
            .clk(_gnd_net_),
            .ce(),
            .sr(_gnd_net_));
    defparam led_io_r_RNO_2_LC_6_7_4.C_ON=1'b0;
    defparam led_io_r_RNO_2_LC_6_7_4.SEQ_MODE=4'b0000;
    defparam led_io_r_RNO_2_LC_6_7_4.LUT_INIT=16'b1000000000000000;
    LogicCell40 led_io_r_RNO_2_LC_6_7_4 (
            .in0(N__754),
            .in1(N__739),
            .in2(N__727),
            .in3(N__724),
            .lcout(blink_counter11_20),
            .ltout(),
            .carryin(_gnd_net_),
            .carryout(),
            .clk(_gnd_net_),
            .ce(),
            .sr(_gnd_net_));
    defparam led_io_r_RNO_1_LC_6_8_1.C_ON=1'b0;
    defparam led_io_r_RNO_1_LC_6_8_1.SEQ_MODE=4'b0000;
    defparam led_io_r_RNO_1_LC_6_8_1.LUT_INIT=16'b1000000000000000;
    LogicCell40 led_io_r_RNO_1_LC_6_8_1 (
            .in0(N__1282),
            .in1(N__1270),
            .in2(N__1258),
            .in3(N__1243),
            .lcout(blink_counter11_19),
            .ltout(),
            .carryin(_gnd_net_),
            .carryout(),
            .clk(_gnd_net_),
            .ce(),
            .sr(_gnd_net_));
    defparam led_io_r_RNO_6_LC_6_8_4.C_ON=1'b0;
    defparam led_io_r_RNO_6_LC_6_8_4.SEQ_MODE=4'b0000;
    defparam led_io_r_RNO_6_LC_6_8_4.LUT_INIT=16'b1000000000000000;
    LogicCell40 led_io_r_RNO_6_LC_6_8_4 (
            .in0(N__1225),
            .in1(N__1213),
            .in2(N__1201),
            .in3(N__1185),
            .lcout(blink_counter11_16),
            .ltout(),
            .carryin(_gnd_net_),
            .carryout(),
            .clk(_gnd_net_),
            .ce(),
            .sr(_gnd_net_));
    defparam led_io_r_RNO_8_LC_6_8_5.C_ON=1'b0;
    defparam led_io_r_RNO_8_LC_6_8_5.SEQ_MODE=4'b0000;
    defparam led_io_r_RNO_8_LC_6_8_5.LUT_INIT=16'b1000000000000000;
    LogicCell40 led_io_r_RNO_8_LC_6_8_5 (
            .in0(N__1168),
            .in1(N__1156),
            .in2(N__1144),
            .in3(N__1122),
            .lcout(blink_counter11_18),
            .ltout(),
            .carryin(_gnd_net_),
            .carryout(),
            .clk(_gnd_net_),
            .ce(),
            .sr(_gnd_net_));
    defparam led_io_r_RNO_5_LC_6_8_6.C_ON=1'b0;
    defparam led_io_r_RNO_5_LC_6_8_6.SEQ_MODE=4'b0000;
    defparam led_io_r_RNO_5_LC_6_8_6.LUT_INIT=16'b1000000000000000;
    LogicCell40 led_io_r_RNO_5_LC_6_8_6 (
            .in0(N__1102),
            .in1(N__1090),
            .in2(N__1078),
            .in3(N__1062),
            .lcout(blink_counter11_15),
            .ltout(),
            .carryin(_gnd_net_),
            .carryout(),
            .clk(_gnd_net_),
            .ce(),
            .sr(_gnd_net_));
    defparam led_io_r_RNO_7_LC_6_9_3.C_ON=1'b0;
    defparam led_io_r_RNO_7_LC_6_9_3.SEQ_MODE=4'b0000;
    defparam led_io_r_RNO_7_LC_6_9_3.LUT_INIT=16'b1000000000000000;
    LogicCell40 led_io_r_RNO_7_LC_6_9_3 (
            .in0(N__1042),
            .in1(N__1030),
            .in2(N__1018),
            .in3(N__1002),
            .lcout(blink_counter11_17),
            .ltout(),
            .carryin(_gnd_net_),
            .carryout(),
            .clk(_gnd_net_),
            .ce(),
            .sr(_gnd_net_));
    defparam CONSTANT_ONE_LUT4_LC_6_10_0.C_ON=1'b0;
    defparam CONSTANT_ONE_LUT4_LC_6_10_0.SEQ_MODE=4'b0000;
    defparam CONSTANT_ONE_LUT4_LC_6_10_0.LUT_INIT=16'b1111111111111111;
    LogicCell40 CONSTANT_ONE_LUT4_LC_6_10_0 (
            .in0(_gnd_net_),
            .in1(_gnd_net_),
            .in2(_gnd_net_),
            .in3(_gnd_net_),
            .lcout(CONSTANT_ONE_NET),
            .ltout(),
            .carryin(_gnd_net_),
            .carryout(),
            .clk(_gnd_net_),
            .ce(),
            .sr(_gnd_net_));
    defparam led_io_r_RNO_0_LC_7_7_7.C_ON=1'b0;
    defparam led_io_r_RNO_0_LC_7_7_7.SEQ_MODE=4'b0000;
    defparam led_io_r_RNO_0_LC_7_7_7.LUT_INIT=16'b0000000011111111;
    LogicCell40 led_io_r_RNO_0_LC_7_7_7 (
            .in0(_gnd_net_),
            .in1(_gnd_net_),
            .in2(_gnd_net_),
            .in3(N__940),
            .lcout(locked_i),
            .ltout(),
            .carryin(_gnd_net_),
            .carryout(),
            .clk(_gnd_net_),
            .ce(),
            .sr(_gnd_net_));
endmodule // Top
