MichalVarsanyi/VoxLink/Firmware/Vivado/Projects/Vox_Readout_Testing/Vox_Readout_Testing.runs/synth_1/.Xil/Top_propImpl.xdc

set_property SRC_FILE_INFO {cfile:C:/Users/varsa/Desktop/School/5_semester/BachelorProject/VoxLink/Firmware/Vivado/Source/Constraints/Vox_Readout_Testing.xdc rfile:../../../../../Source/Constraints/Vox_Readout_Testing.xdc id:1} [current_design]
set_property src_info {type:XDC file:1 line:6 export:INPUT save:INPUT read:READ} [current_design]
set_property PACKAGE_PIN L17 [get_ports clk_12mhz]
set_property src_info {type:XDC file:1 line:10 export:INPUT save:INPUT read:READ} [current_design]
set_property PACKAGE_PIN A17 [get_ports fpga_led]
set_property src_info {type:XDC file:1 line:23 export:INPUT save:INPUT read:READ} [current_design]
set_property PACKAGE_PIN J17 [get_ports uart_rxd]
set_property src_info {type:XDC file:1 line:26 export:INPUT save:INPUT read:READ} [current_design]
set_property PACKAGE_PIN J18 [get_ports uart_txd]
set_property src_info {type:XDC file:1 line:32 export:INPUT save:INPUT read:READ} [current_design]
set_property PACKAGE_PIN V8 [get_ports vox_clk]
set_property src_info {type:XDC file:1 line:35 export:INPUT save:INPUT read:READ} [current_design]
set_property PACKAGE_PIN W7 [get_ports vox_rxd]
