MichalVarsanyi/VoxLink/Firmware/Lattice/Projects/Core_Module_BringUp/Core_Module_BringUp_Implmnt/sbt/outputs/simulation_netlist/Top_sbt.vhd

-- ******************************************************************************

-- iCEcube Netlister

-- Version:            2020.12.27943

-- Build Date:         Dec  9 2020 18:18:06

-- File Generated:     Apr 23 2026 17:54:58

-- Purpose:            Post-Route Verilog/VHDL netlist for timing simulation

-- Copyright (C) 2006-2010 by Lattice Semiconductor Corp. All rights reserved.

-- ******************************************************************************

-- VHDL file for cell "Top" view "INTERFACE"

library ieee;
use ieee.std_logic_1164.all;
use ieee.std_logic_arith.all;
use ieee.std_logic_unsigned.all;

library ice;
use ice.vcomponent_vital.all;

-- Entity of Top
entity Top is
port (
    led_io : out std_logic;
    clk_12mhz : in std_logic);
end Top;

-- Architecture of Top
-- View name is \INTERFACE\
architecture \INTERFACE\ of Top is

signal \N__1301\ : std_logic;
signal \N__1300\ : std_logic;
signal \N__1299\ : std_logic;
signal \N__1282\ : std_logic;
signal \N__1281\ : std_logic;
signal \N__1278\ : std_logic;
signal \N__1275\ : std_logic;
signal \N__1270\ : std_logic;
signal \N__1269\ : std_logic;
signal \N__1266\ : std_logic;
signal \N__1263\ : std_logic;
signal \N__1258\ : std_logic;
signal \N__1255\ : std_logic;
signal \N__1254\ : std_logic;
signal \N__1251\ : std_logic;
signal \N__1248\ : std_logic;
signal \N__1243\ : std_logic;
signal \N__1242\ : std_logic;
signal \N__1239\ : std_logic;
signal \N__1236\ : std_logic;
signal \N__1231\ : std_logic;
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
signal blink_counter_cry_13 : std_logic;
signal blink_counter_cry_14 : std_logic;
signal blink_counter_cry_15 : std_logic;
signal \bfn_5_9_0_\ : std_logic;
signal blink_counter_cry_16 : std_logic;
signal blink_counter_cry_17 : std_logic;
signal blink_counter_cry_18 : std_logic;
signal blink_counter_cry_19 : std_logic;
signal blink_counter_cry_20 : std_logic;
signal blink_counter_cry_21 : std_logic;
signal blink_counter_cry_22 : std_logic;
signal blink_counter_cry_23 : std_logic;
signal \bfn_5_10_0_\ : std_logic;
signal blink_counter_cry_24 : std_logic;
signal blink_counter_cry_25 : std_logic;
signal clk_12mhz_bufg : std_logic;
signal \GB_BUFFER_clk_12mhz_bufg_THRU_CO\ : std_logic;
signal \blink_counter11_24_cascade_\ : std_logic;
signal \led_io_rZ0\ : std_logic;
signal sys_clk : std_logic;
signal \blink_counterZ0Z_3\ : std_logic;
signal \blink_counterZ0Z_2\ : std_logic;
signal \blink_counterZ0Z_4\ : std_logic;
signal \blink_counterZ0Z_5\ : std_logic;
signal \blink_counterZ0Z_23\ : std_logic;
signal \blink_counterZ0Z_1\ : std_logic;
signal \blink_counter11_14_cascade_\ : std_logic;
signal \blink_counterZ0Z_0\ : std_logic;
signal blink_counter11_20 : std_logic;
signal \blink_counterZ0Z_21\ : std_logic;
signal \blink_counterZ0Z_20\ : std_logic;
signal \blink_counterZ0Z_19\ : std_logic;
signal \blink_counterZ0Z_22\ : std_logic;
signal blink_counter11_19 : std_logic;
signal \blink_counterZ0Z_11\ : std_logic;
signal \blink_counterZ0Z_10\ : std_logic;
signal \blink_counterZ0Z_12\ : std_logic;
signal \blink_counterZ0Z_13\ : std_logic;
signal blink_counter11_16 : std_logic;
signal \blink_counterZ0Z_17\ : std_logic;
signal \blink_counterZ0Z_16\ : std_logic;
signal \blink_counterZ0Z_26\ : std_logic;
signal \blink_counterZ0Z_18\ : std_logic;
signal blink_counter11_18 : std_logic;
signal \blink_counterZ0Z_7\ : std_logic;
signal \blink_counterZ0Z_6\ : std_logic;
signal \blink_counterZ0Z_9\ : std_logic;
signal \blink_counterZ0Z_8\ : std_logic;
signal blink_counter11_15 : std_logic;
signal \blink_counterZ0Z_15\ : std_logic;
signal \blink_counterZ0Z_14\ : std_logic;
signal \blink_counterZ0Z_24\ : std_logic;
signal \blink_counterZ0Z_25\ : std_logic;
signal blink_counter11_17 : std_logic;
signal \CONSTANT_ONE_NET\ : std_logic;
signal locked_g : std_logic;
signal locked_i : std_logic;
signal \_gnd_net_\ : std_logic;

signal clk_12mhz_wire : std_logic;
signal led_io_wire : std_logic;
signal \u_pll_DYNAMICDELAY_wire\ : std_logic_vector(7 downto 0);

begin
    clk_12mhz_wire <= clk_12mhz;
    led_io <= led_io_wire;
    \u_pll_DYNAMICDELAY_wire\ <= \GNDG0\&\GNDG0\&\GNDG0\&\GNDG0\&\GNDG0\&\GNDG0\&\GNDG0\&\GNDG0\;

    \u_pll\ : SB_PLL40_CORE
    generic map (
            DELAY_ADJUSTMENT_MODE_FEEDBACK => "FIXED",
            TEST_MODE => '0',
            SHIFTREG_DIV_MODE => "00",
            PLLOUT_SELECT => "GENCLK",
            FILTER_RANGE => "001",
            FEEDBACK_PATH => "SIMPLE",
            FDA_RELATIVE => "0000",
            FDA_FEEDBACK => "0000",
            ENABLE_ICEGATE => '0',
            DIVR => "0000",
            DIVQ => "011",
            DIVF => "1000010",
            DELAY_ADJUSTMENT_MODE_RELATIVE => "FIXED"
        )
    port map (
            EXTFEEDBACK => '0',
            LATCHINPUTVALUE => '0',
            SCLK => '0',
            SDO => OPEN,
            LOCK => \PLL_BUFFER_u_pll_LOCK_THRU_CO\,
            PLLOUTCORE => sys_clkout,
            REFERENCECLK => \N__874\,
            RESETB => \N__968\,
            BYPASS => \GNDG0\,
            SDI => '0',
            DYNAMICDELAY => \u_pll_DYNAMICDELAY_wire\,
            PLLOUTGLOBAL => OPEN
        );

    \clk_12mhz_ibuf_iopad\ : IO_PAD
    generic map (
            IO_STANDARD => "SB_LVCMOS",
            PULLUP => '0'
        )
    port map (
            OE => \N__1301\,
            DIN => \N__1300\,
            DOUT => \N__1299\,
            PACKAGEPIN => clk_12mhz_wire
        );

    \clk_12mhz_ibuf_preio\ : PRE_IO
    generic map (
            NEG_TRIGGER => '0',
            PIN_TYPE => "000001"
        )
    port map (
            PADOEN => \N__1301\,
            PADOUT => \N__1300\,
            PADIN => \N__1299\,
            CLOCKENABLE => 'H',
            DOUT1 => '0',
            OUTPUTENABLE => '0',
            DIN0 => clk_12mhz_c,
            DOUT0 => '0',
            INPUTCLK => '0',
            LATCHINPUTVALUE => '0',
            DIN1 => OPEN,
            OUTPUTCLK => '0'
        );

    \I__288\ : InMux
    port map (
            O => \N__1282\,
            I => \N__1278\
        );

    \I__287\ : InMux
    port map (
            O => \N__1281\,
            I => \N__1275\
        );

    \I__286\ : LocalMux
    port map (
            O => \N__1278\,
            I => \blink_counterZ0Z_21\
        );

    \I__285\ : LocalMux
    port map (
            O => \N__1275\,
            I => \blink_counterZ0Z_21\
        );

    \I__284\ : InMux
    port map (
            O => \N__1270\,
            I => \N__1266\
        );

    \I__283\ : InMux
    port map (
            O => \N__1269\,
            I => \N__1263\
        );

    \I__282\ : LocalMux
    port map (
            O => \N__1266\,
            I => \blink_counterZ0Z_20\
        );

    \I__281\ : LocalMux
    port map (
            O => \N__1263\,
            I => \blink_counterZ0Z_20\
        );

    \I__280\ : CascadeMux
    port map (
            O => \N__1258\,
            I => \N__1255\
        );

    \I__279\ : InMux
    port map (
            O => \N__1255\,
            I => \N__1251\
        );

    \I__278\ : InMux
    port map (
            O => \N__1254\,
            I => \N__1248\
        );

    \I__277\ : LocalMux
    port map (
            O => \N__1251\,
            I => \blink_counterZ0Z_19\
        );

    \I__276\ : LocalMux
    port map (
            O => \N__1248\,
            I => \blink_counterZ0Z_19\
        );

    \I__275\ : InMux
    port map (
            O => \N__1243\,
            I => \N__1239\
        );

    \I__274\ : InMux
    port map (
            O => \N__1242\,
            I => \N__1236\
        );

    \I__273\ : LocalMux
    port map (
            O => \N__1239\,
            I => \blink_counterZ0Z_22\
        );

    \I__272\ : LocalMux
    port map (
            O => \N__1236\,
            I => \blink_counterZ0Z_22\
        );

    \I__271\ : InMux
    port map (
            O => \N__1231\,
            I => \N__1228\
        );

    \I__270\ : LocalMux
    port map (
            O => \N__1228\,
            I => blink_counter11_19
        );

    \I__269\ : InMux
    port map (
            O => \N__1225\,
            I => \N__1221\
        );

    \I__268\ : InMux
    port map (
            O => \N__1224\,
            I => \N__1218\
        );

    \I__267\ : LocalMux
    port map (
            O => \N__1221\,
            I => \blink_counterZ0Z_11\
        );

    \I__266\ : LocalMux
    port map (
            O => \N__1218\,
            I => \blink_counterZ0Z_11\
        );

    \I__265\ : InMux
    port map (
            O => \N__1213\,
            I => \N__1209\
        );

    \I__264\ : InMux
    port map (
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
    port map (
            O => \N__598\,
            I => \N__595\
        );

    \I__59\ : Odrv12
    port map (
            O => \N__595\,
            I => locked
        );

    \I__58\ : InMux
    port map (
            O => \N__592\,
            I => \bfn_5_7_0_\
        );

    \I__57\ : InMux
    port map (
            O => \N__589\,
            I => blink_counter_cry_0
        );

    \I__56\ : InMux
    port map (
            O => \N__586\,
            I => blink_counter_cry_1
        );

    \I__55\ : InMux
    port map (
            O => \N__583\,
            I => blink_counter_cry_2
        );

    \I__54\ : InMux
    port map (
            O => \N__580\,
            I => blink_counter_cry_3
        );

    \I__53\ : InMux
    port map (
            O => \N__577\,
            I => blink_counter_cry_4
        );

    \IN_MUX_bfv_5_7_0_\ : ICE_CARRY_IN_MUX
    generic map (
            C_INIT => "01"
        )
    port map (
            carryinitin => '0',
            carryinitout => \bfn_5_7_0_\
        );

    \IN_MUX_bfv_5_8_0_\ : ICE_CARRY_IN_MUX
    generic map (
            C_INIT => "10"
        )
    port map (
            carryinitin => blink_counter_cry_7,
            carryinitout => \bfn_5_8_0_\
        );

    \IN_MUX_bfv_5_9_0_\ : ICE_CARRY_IN_MUX
    generic map (
            C_INIT => "10"
        )
    port map (
            carryinitin => blink_counter_cry_15,
            carryinitout => \bfn_5_9_0_\
        );

    \IN_MUX_bfv_5_10_0_\ : ICE_CARRY_IN_MUX
    generic map (
            C_INIT => "10"
        )
    port map (
            carryinitin => blink_counter_cry_23,
            carryinitout => \bfn_5_10_0_\
        );

    \GND\ : GND
    port map (
            Y => \GNDG0\
        );

    \clk_in\ : ICE_GB
    port map (
            USERSIGNALTOGLOBALBUFFER => \N__652\,
            GLOBALBUFFEROUTPUT => clk_12mhz_bufg
        );

    \led_driver\ : SB_RGBA_DRV
    generic map (
            CURRENT_MODE => "0b1",
            RGB2_CURRENT => "0b000000",
            RGB1_CURRENT => "0b000000",
            RGB0_CURRENT => "0b000001"
        )
    port map (
            RGBLEDEN => \N__982\,
            RGB2PWM => '0',
            RGB1 => OPEN,
            CURREN => \N__981\,
            RGB2 => OPEN,
            RGB1PWM => '0',
            RGB0PWM => \N__856\,
            RGB0 => led_io_wire
        );

    \u_pll_RNISDD6\ : ICE_GB
    port map (
            USERSIGNALTOGLOBALBUFFER => \N__607\,
            GLOBALBUFFEROUTPUT => locked_g
        );

    \VCC\ : VCC
    port map (
            Y => \VCCG0\
        );

    \clk_pll\ : ICE_GB
    port map (
            USERSIGNALTOGLOBALBUFFER => \N__631\,
            GLOBALBUFFEROUTPUT => sys_clk
        );

    \GND_Inst\ : GND
    port map (
            Y => \_gnd_net_\
        );

    \PLL_BUFFER_u_pll_LOCK_THRU_LUT4_0_LC_1_1_0\ : LogicCell40
    generic map (
            C_ON => '0',
            SEQ_MODE => "0000",
            LUT_INIT => "1111111100000000"
        )
    port map (
            in0 => \_gnd_net_\,
            in1 => \_gnd_net_\,
            in2 => \_gnd_net_\,
            in3 => \N__613\,
            lcout => locked,
            ltout => OPEN,
            carryin => \_gnd_net_\,
            carryout => OPEN,
            clk => \_gnd_net_\,
            ce => 'H',
            sr => \_gnd_net_\
        );

    \blink_counter_0_LC_5_7_0\ : LogicCell40
    generic map (
            C_ON => '1',
            SEQ_MODE => "1000",
            LUT_INIT => "1001100101100110"
        )
    port map (
            in0 => \_gnd_net_\,
            in1 => \N__723\,
            in2 => \_gnd_net_\,
            in3 => \N__592\,
            lcout => \blink_counterZ0Z_0\,
            ltout => OPEN,
            carryin => \bfn_5_7_0_\,
            carryout => blink_counter_cry_0,
            clk => \N__828\,
            ce => \N__930\,
            sr => \_gnd_net_\
        );

    \blink_counter_1_LC_5_7_1\ : LogicCell40
    generic map (
            C_ON => '1',
            SEQ_MODE => "1000",
            LUT_INIT => "1001100101100110"
        )
    port map (
            in0 => \_gnd_net_\,
            in1 => \N__738\,
            in2 => \_gnd_net_\,
            in3 => \N__589\,
            lcout => \blink_counterZ0Z_1\,
            ltout => OPEN,
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
            in2 => \_gnd_net_\,
            in3 => \N__940\,
            lcout => locked_i,
            ltout => OPEN,
            carryin => \_gnd_net_\,
            carryout => OPEN,
            clk => \_gnd_net_\,
            ce => 'H',
            sr => \_gnd_net_\
        );
end \INTERFACE\;
