MichalVarsanyi/VoxLink/Firmware/Vivado/Projects/VoxLink_Controller/VoxLink_Controller.cache/ip/2024.1/a/6/a6a7915305ae47ab/blk_mem_gen_0_sim_netlist.v

// Copyright 1986-2022 Xilinx, Inc. All Rights Reserved.
// Copyright 2022-2024 Advanced Micro Devices, Inc. All Rights Reserved.
// --------------------------------------------------------------------------------
// Tool Version: Vivado v.2024.1 (win64) Build 5076996 Wed May 22 18:37:14 MDT 2024
// Date        : Tue May  5 16:36:00 2026
// Host        : LAPTOP-GK6ER3TV running 64-bit major release  (build 9200)
// Command     : write_verilog -force -mode funcsim -rename_top decalper_eb_ot_sdeen_pot_pi_dehcac_xnilix -prefix
//               decalper_eb_ot_sdeen_pot_pi_dehcac_xnilix_ blk_mem_gen_0_sim_netlist.v
// Design      : blk_mem_gen_0
// Purpose     : This verilog netlist is a functional simulation representation of the design and should not be modified
//               or synthesized. This netlist cannot be used for SDF annotated simulation.
// Device      : xc7a35tcsg324-1
// --------------------------------------------------------------------------------
`timescale 1 ps / 1 ps

(* CHECK_LICENSE_TYPE = "blk_mem_gen_0,blk_mem_gen_v8_4_8,{}" *) (* downgradeipidentifiedwarnings = "yes" *) (* x_core_info = "blk_mem_gen_v8_4_8,Vivado 2024.1" *) 
(* NotValidForBitStream *)
module decalper_eb_ot_sdeen_pot_pi_dehcac_xnilix
   (clka,
    ena,
    wea,
    addra,
    dina,
    douta);
  (* x_interface_info = "xilinx.com:interface:bram:1.0 BRAM_PORTA CLK" *) (* x_interface_parameter = "XIL_INTERFACENAME BRAM_PORTA, MEM_ADDRESS_MODE BYTE_ADDRESS, MEM_SIZE 8192, MEM_WIDTH 32, MEM_ECC NONE, MASTER_TYPE OTHER, READ_LATENCY 1" *) input clka;
  (* x_interface_info = "xilinx.com:interface:bram:1.0 BRAM_PORTA EN" *) input ena;
  (* x_interface_info = "xilinx.com:interface:bram:1.0 BRAM_PORTA WE" *) input [0:0]wea;
  (* x_interface_info = "xilinx.com:interface:bram:1.0 BRAM_PORTA ADDR" *) input [6:0]addra;
  (* x_interface_info = "xilinx.com:interface:bram:1.0 BRAM_PORTA DIN" *) input [111:0]dina;
  (* x_interface_info = "xilinx.com:interface:bram:1.0 BRAM_PORTA DOUT" *) output [111:0]douta;

  wire [6:0]addra;
  wire clka;
  wire [111:0]dina;
  wire [111:0]douta;
  wire ena;
  wire [0:0]wea;
  wire NLW_U0_dbiterr_UNCONNECTED;
  wire NLW_U0_rsta_busy_UNCONNECTED;
  wire NLW_U0_rstb_busy_UNCONNECTED;
  wire NLW_U0_s_axi_arready_UNCONNECTED;
  wire NLW_U0_s_axi_awready_UNCONNECTED;
  wire NLW_U0_s_axi_bvalid_UNCONNECTED;
  wire NLW_U0_s_axi_dbiterr_UNCONNECTED;
  wire NLW_U0_s_axi_rlast_UNCONNECTED;
  wire NLW_U0_s_axi_rvalid_UNCONNECTED;
  wire NLW_U0_s_axi_sbiterr_UNCONNECTED;
  wire NLW_U0_s_axi_wready_UNCONNECTED;
  wire NLW_U0_sbiterr_UNCONNECTED;
  wire [111:0]NLW_U0_doutb_UNCONNECTED;
  wire [6:0]NLW_U0_rdaddrecc_UNCONNECTED;
  wire [3:0]NLW_U0_s_axi_bid_UNCONNECTED;
  wire [1:0]NLW_U0_s_axi_bresp_UNCONNECTED;
  wire [6:0]NLW_U0_s_axi_rdaddrecc_UNCONNECTED;
  wire [111:0]NLW_U0_s_axi_rdata_UNCONNECTED;
  wire [3:0]NLW_U0_s_axi_rid_UNCONNECTED;
  wire [1:0]NLW_U0_s_axi_rresp_UNCONNECTED;

  (* C_ADDRA_WIDTH = "7" *) 
  (* C_ADDRB_WIDTH = "7" *) 
  (* C_ALGORITHM = "1" *) 
  (* C_AXI_ID_WIDTH = "4" *) 
  (* C_AXI_SLAVE_TYPE = "0" *) 
  (* C_AXI_TYPE = "1" *) 
  (* C_BYTE_SIZE = "9" *) 
  (* C_COMMON_CLK = "0" *) 
  (* C_COUNT_18K_BRAM = "0" *) 
  (* C_COUNT_36K_BRAM = "2" *) 
  (* C_CTRL_ECC_ALGO = "NONE" *) 
  (* C_DEFAULT_DATA = "0" *) 
  (* C_DISABLE_WARN_BHV_COLL = "0" *) 
  (* C_DISABLE_WARN_BHV_RANGE = "0" *) 
  (* C_ELABORATION_DIR = "./" *) 
  (* C_ENABLE_32BIT_ADDRESS = "0" *) 
  (* C_EN_DEEPSLEEP_PIN = "0" *) 
  (* C_EN_ECC_PIPE = "0" *) 
  (* C_EN_RDADDRA_CHG = "0" *) 
  (* C_EN_RDADDRB_CHG = "0" *) 
  (* C_EN_SAFETY_CKT = "0" *) 
  (* C_EN_SHUTDOWN_PIN = "0" *) 
  (* C_EN_SLEEP_PIN = "0" *) 
  (* C_EST_POWER_SUMMARY = "Estimated Power for IP     :     12.8379 mW" *) 
  (* C_FAMILY = "artix7" *) 
  (* C_HAS_AXI_ID = "0" *) 
  (* C_HAS_ENA = "1" *) 
  (* C_HAS_ENB = "0" *) 
  (* C_HAS_INJECTERR = "0" *) 
  (* C_HAS_MEM_OUTPUT_REGS_A = "1" *) 
  (* C_HAS_MEM_OUTPUT_REGS_B = "0" *) 
  (* C_HAS_MUX_OUTPUT_REGS_A = "0" *) 
  (* C_HAS_MUX_OUTPUT_REGS_B = "0" *) 
  (* C_HAS_REGCEA = "0" *) 
  (* C_HAS_REGCEB = "0" *) 
  (* C_HAS_RSTA = "0" *) 
  (* C_HAS_RSTB = "0" *) 
  (* C_HAS_SOFTECC_INPUT_REGS_A = "0" *) 
  (* C_HAS_SOFTECC_OUTPUT_REGS_B = "0" *) 
  (* C_INITA_VAL = "0" *) 
  (* C_INITB_VAL = "0" *) 
  (* C_INIT_FILE = "blk_mem_gen_0.mem" *) 
  (* C_INIT_FILE_NAME = "no_coe_file_loaded" *) 
  (* C_INTERFACE_TYPE = "0" *) 
  (* C_LOAD_INIT_FILE = "0" *) 
  (* C_MEM_TYPE = "0" *) 
  (* C_MUX_PIPELINE_STAGES = "0" *) 
  (* C_PRIM_TYPE = "1" *) 
  (* C_READ_DEPTH_A = "128" *) 
  (* C_READ_DEPTH_B = "128" *) 
  (* C_READ_LATENCY_A = "1" *) 
  (* C_READ_LATENCY_B = "1" *) 
  (* C_READ_WIDTH_A = "112" *) 
  (* C_READ_WIDTH_B = "112" *) 
  (* C_RSTRAM_A = "0" *) 
  (* C_RSTRAM_B = "0" *) 
  (* C_RST_PRIORITY_A = "CE" *) 
  (* C_RST_PRIORITY_B = "CE" *) 
  (* C_SIM_COLLISION_CHECK = "ALL" *) 
  (* C_USE_BRAM_BLOCK = "0" *) 
  (* C_USE_BYTE_WEA = "0" *) 
  (* C_USE_BYTE_WEB = "0" *) 
  (* C_USE_DEFAULT_DATA = "0" *) 
  (* C_USE_ECC = "0" *) 
  (* C_USE_SOFTECC = "0" *) 
  (* C_USE_URAM = "0" *) 
  (* C_WEA_WIDTH = "1" *) 
  (* C_WEB_WIDTH = "1" *) 
  (* C_WRITE_DEPTH_A = "128" *) 
  (* C_WRITE_DEPTH_B = "128" *) 
  (* C_WRITE_MODE_A = "WRITE_FIRST" *) 
  (* C_WRITE_MODE_B = "WRITE_FIRST" *) 
  (* C_WRITE_WIDTH_A = "112" *) 
  (* C_WRITE_WIDTH_B = "112" *) 
  (* C_XDEVICEFAMILY = "artix7" *) 
  (* downgradeipidentifiedwarnings = "yes" *) 
  (* is_du_within_envelope = "true" *) 
  decalper_eb_ot_sdeen_pot_pi_dehcac_xnilix_blk_mem_gen_v8_4_8 U0
       (.addra(addra),
        .addrb({1'b0,1'b0,1'b0,1'b0,1'b0,1'b0,1'b0}),
        .clka(clka),
        .clkb(1'b0),
        .dbiterr(NLW_U0_dbiterr_UNCONNECTED),
        .deepsleep(1'b0),
        .dina(dina),
        .dinb({1'b0,1'b0,1'b0,1'b0,1'b0,1'b0,1'b0,1'b0,1'b0,1'b0,1'b0,1'b0,1'b0,1'b0,1'b0,1'b0,1'b0,1'b0,1'b0,1'b0,1'b0,1'b0,1'b0,1'b0,1'b0,1'b0,1'b0,1'b0,1'b0,1'b0,1'b0,1'b0,1'b0,1'b0,1'b0,1'b0,1'b0,1'b0,1'b0,1'b0,1'b0,1'b0,1'b0,1'b0,1'b0,1'b0,1'b0,1'b0,1'b0,1'b0,1'b0,1'b0,1'b0,1'b0,1'b0,1'b0,1'b0,1'b0,1'b0,1'b0,1'b0,1'b0,1'b0,1'b0,1'b0,1'b0,1'b0,1'b0,1'b0,1'b0,1'b0,1'b0,1'b0,1'b0,1'b0,1'b0,1'b0,1'b0,1'b0,1'b0,1'b0,1'b0,1'b0,1'b0,1'b0,1'b0,1'b0,1'b0,1'b0,1'b0,1'b0,1'b0,1'b0,1'b0,1'b0,1'b0,1'b0,1'b0,1'b0,1'b0,1'b0,1'b0,1'b0,1'b0,1'b0,1'b0,1'b0,1'b0,1'b0,1'b0,1'b0,1'b0}),
        .douta(douta),
        .doutb(NLW_U0_doutb_UNCONNECTED[111:0]),
        .eccpipece(1'b0),
        .ena(ena),
        .enb(1'b0),
        .injectdbiterr(1'b0),
        .injectsbiterr(1'b0),
        .rdaddrecc(NLW_U0_rdaddrecc_UNCONNECTED[6:0]),
        .regcea(1'b1),
        .regceb(1'b1),
        .rsta(1'b0),
        .rsta_busy(NLW_U0_rsta_busy_UNCONNECTED),
        .rstb(1'b0),
        .rstb_busy(NLW_U0_rstb_busy_UNCONNECTED),
        .s_aclk(1'b0),
        .s_aresetn(1'b0),
        .s_axi_araddr({1'b0,1'b0,1'b0,1'b0,1'b0,1'b0,1'b0,1'b0,1'b0,1'b0,1'b0,1'b0,1'b0,1'b0,1'b0,1'b0,1'b0,1'b0,1'b0,1'b0,1'b0,1'b0,1'b0,1'b0,1'b0,1'b0,1'b0,1'b0,1'b0,1'b0,1'b0,1'b0}),
        .s_axi_arburst({1'b0,1'b0}),
        .s_axi_arid({1'b0,1'b0,1'b0,1'b0}),
        .s_axi_arlen({1'b0,1'b0,1'b0,1'b0,1'b0,1'b0,1'b0,1'b0}),
        .s_axi_arready(NLW_U0_s_axi_arready_UNCONNECTED),
        .s_axi_arsize({1'b0,1'b0,1'b0}),
        .s_axi_arvalid(1'b0),
        .s_axi_awaddr({1'b0,1'b0,1'b0,1'b0,1'b0,1'b0,1'b0,1'b0,1'b0,1'b0,1'b0,1'b0,1'b0,1'b0,1'b0,1'b0,1'b0,1'b0,1'b0,1'b0,1'b0,1'b0,1'b0,1'b0,1'b0,1'b0,1'b0,1'b0,1'b0,1'b0,1'b0,1'b0}),
        .s_axi_awburst({1'b0,1'b0}),
        .s_axi_awid({1'b0,1'b0,1'b0,1'b0}),
        .s_axi_awlen({1'b0,1'b0,1'b0,1'b0,1'b0,1'b0,1'b0,1'b0}),
        .s_axi_awready(NLW_U0_s_axi_awready_UNCONNECTED),
        .s_axi_awsize({1'b0,1'b0,1'b0}),
        .s_axi_awvalid(1'b0),
        .s_axi_bid(NLW_U0_s_axi_bid_UNCONNECTED[3:0]),
        .s_axi_bready(1'b0),
        .s_axi_bresp(NLW_U0_s_axi_bresp_UNCONNECTED[1:0]),
        .s_axi_bvalid(NLW_U0_s_axi_bvalid_UNCONNECTED),
        .s_axi_dbiterr(NLW_U0_s_axi_dbiterr_UNCONNECTED),
        .s_axi_injectdbiterr(1'b0),
        .s_axi_injectsbiterr(1'b0),
        .s_axi_rdaddrecc(NLW_U0_s_axi_rdaddrecc_UNCONNECTED[6:0]),
        .s_axi_rdata(NLW_U0_s_axi_rdata_UNCONNECTED[111:0]),
        .s_axi_rid(NLW_U0_s_axi_rid_UNCONNECTED[3:0]),
        .s_axi_rlast(NLW_U0_s_axi_rlast_UNCONNECTED),
        .s_axi_rready(1'b0),
        .s_axi_rresp(NLW_U0_s_axi_rresp_UNCONNECTED[1:0]),
        .s_axi_rvalid(NLW_U0_s_axi_rvalid_UNCONNECTED),
        .s_axi_sbiterr(NLW_U0_s_axi_sbiterr_UNCONNECTED),
        .s_axi_wdata({1'b0,1'b0,1'b0,1'b0,1'b0,1'b0,1'b0,1'b0,1'b0,1'b0,1'b0,1'b0,1'b0,1'b0,1'b0,1'b0,1'b0,1'b0,1'b0,1'b0,1'b0,1'b0,1'b0,1'b0,1'b0,1'b0,1'b0,1'b0,1'b0,1'b0,1'b0,1'b0,1'b0,1'b0,1'b0,1'b0,1'b0,1'b0,1'b0,1'b0,1'b0,1'b0,1'b0,1'b0,1'b0,1'b0,1'b0,1'b0,1'b0,1'b0,1'b0,1'b0,1'b0,1'b0,1'b0,1'b0,1'b0,1'b0,1'b0,1'b0,1'b0,1'b0,1'b0,1'b0,1'b0,1'b0,1'b0,1'b0,1'b0,1'b0,1'b0,1'b0,1'b0,1'b0,1'b0,1'b0,1'b0,1'b0,1'b0,1'b0,1'b0,1'b0,1'b0,1'b0,1'b0,1'b0,1'b0,1'b0,1'b0,1'b0,1'b0,1'b0,1'b0,1'b0,1'b0,1'b0,1'b0,1'b0,1'b0,1'b0,1'b0,1'b0,1'b0,1'b0,1'b0,1'b0,1'b0,1'b0,1'b0,1'b0,1'b0,1'b0}),
        .s_axi_wlast(1'b0),
        .s_axi_wready(NLW_U0_s_axi_wready_UNCONNECTED),
        .s_axi_wstrb(1'b0),
        .s_axi_wvalid(1'b0),
        .sbiterr(NLW_U0_sbiterr_UNCONNECTED),
        .shutdown(1'b0),
        .sleep(1'b0),
        .wea(wea),
        .web(1'b0));
endmodule
`pragma protect begin_protected
`pragma protect version = 1
`pragma protect encrypt_agent = "XILINX"
`pragma protect encrypt_agent_info = "Xilinx Encryption Tool 2024.1"
`pragma protect key_keyowner="Synopsys", key_keyname="SNPS-VCS-RSA-2", key_method="rsa"
`pragma protect encoding = (enctype="BASE64", line_length=76, bytes=128)
`pragma protect key_block
RSqbsRZSIb+QlYJMfFv1T7uHQ7PiCEXQkl687MHGm2LgPB15GIYcPmqKUSXgtkLsIFes91PTAyyB
9H9cyY4ZUxedcRg/9ZOB5pm3zPqAbcvGPmg1ivMhr/MlS19t5lYKM2tQo+0Yd+arJXlVZu2BMnvn
+I3G9t9tJuWUIWKjI+I=

`pragma protect key_keyowner="Aldec", key_keyname="ALDEC15_001", key_method="rsa"
`pragma protect encoding = (enctype="BASE64", line_length=76, bytes=256)
`pragma protect key_block
VRSQ05ZaB6bIhFIQ823mTvlJaG9+5iW5C3+KxGjq0sq9ziCshKOLpOGPDMmOWDqA4uBaxC5IKISr
w8+A8mqbYjXo5m1g8sGjNaETS0HKJsK+l5Y++tN4IEUs+DwxgrPR/+LWtChuOzVkfC7BG3LVUEMj
zM3GAyGcXGJ3sdBItZAfsevyiy7kr4Fw+nk2hWytGteu1NZk3VzPE7KQHLkOlHBPXf6P0j8LpKcr
2oNDgQ/WaEmg6OOvFeJuaWDaee8Sn6wKP/caMyoGdSeczsPtRrJeoSRlbNHlxhCv7zg+Cn2AgwrR
PTqGsMrkhv9U0sq+waS0CmwChsk4WB7RspGYUg==

`pragma protect key_keyowner="Mentor Graphics Corporation", key_keyname="MGC-VELOCE-RSA", key_method="rsa"
`pragma protect encoding = (enctype="BASE64", line_length=76, bytes=128)
`pragma protect key_block
tNziOjCznlvIl4dadmB9r23Duf+HQHWOuHmupEU3PJxrazHVtZdNKspG9sRXhF9mjbpnSiKYCdFK
Jr9W/dxUid36faFIPKQazVTuOiE0hkzVQAGpYxXjT/ITB/9EFBvgvP5L3EAhHv32x6MA1vkFSI7x
HrZ09YNFEF6T7DPTZE4=

`pragma protect key_keyowner="Mentor Graphics Corporation", key_keyname="MGC-VERIF-SIM-RSA-2", key_method="rsa"
`pragma protect encoding = (enctype="BASE64", line_length=76, bytes=256)
`pragma protect key_block
QCYfxgkUHlX1cre1q9aS3sVDIOX36YBK4ZwJXAVUwA6f1OQ77XibjpWJHt5FK9F0PcYp/j21pqzO
BRdkDcFLVAjxER4J5t5iMVhoeMk+3fpiKfYrm4WFl1ygsJsfFJP0jqO1OkjC8iFBtm3n6b7CTl1o
cjBbcBp8UgW6E8rf5inXA0dRqybnyxKJSnMFYLinvpVU6QEc4OKO7mi/i/s9p/efiP+CdQf0yDRU
Fw7o7x0D7tjBv943g5L+4wGZ2JYU+ISqn4Ajxy/bWTTJDe6T/15evhngS61MC8Xjamzc4YLZBP8o
ShfSLoeZeO+Hk5n3xzJRghM0DQ6Sj7NqXFY68w==

`pragma protect key_keyowner="Real Intent", key_keyname="RI-RSA-KEY-1", key_method="rsa"
`pragma protect encoding = (enctype="BASE64", line_length=76, bytes=256)
`pragma protect key_block
Uy8FDDy3dZQGAnMQV0HBesEs+/oZdaq35Kj1PGhy9J/+EBZm0nhhQgYtku8tWABW2jKAC1GtNTvo
uReQyr1hteMxTbD5OIuqv86eb1hXZVENlZ7ichG8auUjkeHAkaSYNbHOuDLIhSqHEL67XbcZ9zPG
1JOY3+VONSww0KYPcQbGSo/2DaC5C0Y+mZODRfJ4+b0WXjce6UaJetilBc3VtqqmodIM2d3HDawF
R0xVJfHj86rXmUkY+SNUw60zsV6raCY6G3k/rXpei1d6zn8tCThkKG5fwiWY8zA7kRdTFIlVKP9h
fb6kfzRBRT/BgVQ8d4RgEcEVV8m3u/Mf4KIlTw==

`pragma protect key_keyowner="Xilinx", key_keyname="xilinxt_2023_11", key_method="rsa"
`pragma protect encoding = (enctype="BASE64", line_length=76, bytes=256)
`pragma protect key_block
Pk1GeRlkUK9lt6DVXYVdtOABlzDEWQDcBsP/p+Wo5HaglDLG5b8gk08xTP3IcJ1RKcfuARPMGO2s
/VqFbnVADV90T1rhjIuWMcBnzYQK/ALUvwv11Uju9Gn0fvPIz52l3QBnpjHI1nlsFB7WeqkzVfHZ
tg9gO9bPHjHLjVd9BzH6McrEWY5RkZ0UBy0Fmh/SownJX1b0YGE7LdwKydEMEpyvb28bwTOwfEv/
4RtsfYtEvTjo6e1ZBm66D9IQmKUu32wzTfn5bFZHdyjZg6+HcTzvHMtQX2+AggXfP6FsO2/83qkb
0bfj226fnLhr32dJxtsaJS5OR63GYtzDJ05ITA==

`pragma protect key_keyowner="Metrics Technologies Inc.", key_keyname="DSim", key_method="rsa"
`pragma protect encoding = (enctype="BASE64", line_length=76, bytes=256)
`pragma protect key_block
LCfWqKmUoUSVOTKNAl5p8n1hfz7SMU2kDOUMBjsDncgSFqiu2zUy1I6GSDrVnF/2umJG5/mWcpvi
rQaFJOlrJ8DNctSuavdlopRAwTMsVi6dAlNGrAawSiDIxtI3tN3MDVdMiH5H+pJMqMt59yXneyCf
2RRSRz2sUQK/aj0lXlqKjVJzVbk8HaBQ8akBJF4iWSMK4foIzJ6iO1EupYovuW6uEiO7jQRWezlW
pbbDenOHHWbfinuX5cbkjpTKHGsEKct65q+ZXJp60m3sconSK3Y2eLQxusuJ1FHDJ4GGKO8mEzCv
3cfGdXX3pVL81OfGO/JD1aMs9H98CO5ssbHqlw==

`pragma protect key_keyowner="Atrenta", key_keyname="ATR-SG-RSA-1", key_method="rsa"
`pragma protect encoding = (enctype="BASE64", line_length=76, bytes=384)
`pragma protect key_block
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

`pragma protect key_keyowner="Cadence Design Systems.", key_keyname="CDS_RSA_KEY_VER_1", key_method="rsa"
`pragma protect encoding = (enctype="BASE64", line_length=76, bytes=256)
`pragma protect key_block
gj+uMxV+tK4Di7pgSOE82FOBeWmUB1A7OKFOSMUW3qrmQ4/YhryfHMlWPxfAq8avQL7tnBTnRFEg
czbErdIcNzYjrM7Qq00QC/mTqmeQX4/apbqGvN+rwK4RR5oj22wfTib/UQNEQX6fbpi6PtmAeUR9
eShsfq+YWcf7z2Zw4Q+o4+E6m4/3CzU68vglNpzNsJ8S9/8XpdIrvAA/WRAX6OEOC4wlNIKDZsq/
+zMbFgSzN1rP844I/CDmxYM0NIzBWWhYBkPfJyQyigmUoXb84lDip0/Dmnq4EHvu7D/tZNnDl5st
JpftRfEpT6S8e/5MBeKUuhbfg6etHo/oFZvPKQ==

`pragma protect key_keyowner="Synplicity", key_keyname="SYNP15_1", key_method="rsa"
`pragma protect encoding = (enctype="BASE64", line_length=76, bytes=256)
`pragma protect key_block
aWTy3xv6SqKsldtLS2gY4KrTS8U+KtFNRHS314f6EYZy1MHE9t7oICJ8eNB8up8A+odoE23N3fJb
1alhaadeRWU2GjlIiK1LjZ5PQw+jb1u1GWtRiY+TcTlD75XUlqwykVBrCDfm565DmgZjZle9T3/t
WEfLo+m/8GfBe8trVnoftsk/XI00BMFXRzw8doPGDhNECS1NUrLebryb9iO5Hf4A/40dtslTARsR
nicN0KoIIyiQ+QzliqyXU/8VjS45inON8R0Kv9Qx46EXUp7bds5uQ7QycRhpLG0IPnMIweudU67w
eQmpHJzvZKBCZks/R0OafZx44H6Jib2+QazBCw==

`pragma protect key_keyowner="Mentor Graphics Corporation", key_keyname="MGC-PREC-RSA", key_method="rsa"
`pragma protect encoding = (enctype="BASE64", line_length=76, bytes=256)
`pragma protect key_block
UGdPiChIPj1lSozqzCQx17Bi+8FWSuMUMzXUkDLH5zcP1t8tZLzh4CU4WAR8lmJxn8gH763fLp5c
RYU6zA0yxHzl2ksc5YRU1XEfQQT9ha8fQnz+18wVKcsa5UIOfMbGDwnS9yfX59ntG8CB0uF8bJKE
y1CS6U/1Stfs1w2mF94iDxI2n2GJlb1UPtWpmxMBI88hY0GktTPXP2Y7JKl8zRl/Lq0wIF8pHwXk
B4nOgKm6hfzPj0xZ6E/TuER/JE3fy8RSm24IlL/CUgpReEslEOYjQ4EKKZRG9/fxg26utQWW9p+G
fWVU53qrFGzBhKQ96Paj1ROkv6hDHyUb6n7uSw==

`pragma protect data_method = "AES128-CBC"
`pragma protect encoding = (enctype = "BASE64", line_length = 76, bytes = 53280)
`pragma protect data_block
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
`pragma protect end_protected
`ifndef GLBL
`define GLBL
`timescale  1 ps / 1 ps

module glbl ();

    parameter ROC_WIDTH = 100000;
    parameter TOC_WIDTH = 0;
    parameter GRES_WIDTH = 10000;
    parameter GRES_START = 10000;

//--------   STARTUP Globals --------------
    wire GSR;
    wire GTS;
    wire GWE;
    wire PRLD;
    wire GRESTORE;
    tri1 p_up_tmp;
    tri (weak1, strong0) PLL_LOCKG = p_up_tmp;

    wire PROGB_GLBL;
    wire CCLKO_GLBL;
    wire FCSBO_GLBL;
    wire [3:0] DO_GLBL;
    wire [3:0] DI_GLBL;
   
    reg GSR_int;
    reg GTS_int;
    reg PRLD_int;
    reg GRESTORE_int;

//--------   JTAG Globals --------------
    wire JTAG_TDO_GLBL;
    wire JTAG_TCK_GLBL;
    wire JTAG_TDI_GLBL;
    wire JTAG_TMS_GLBL;
    wire JTAG_TRST_GLBL;

    reg JTAG_CAPTURE_GLBL;
    reg JTAG_RESET_GLBL;
    reg JTAG_SHIFT_GLBL;
    reg JTAG_UPDATE_GLBL;
    reg JTAG_RUNTEST_GLBL;

    reg JTAG_SEL1_GLBL = 0;
    reg JTAG_SEL2_GLBL = 0 ;
    reg JTAG_SEL3_GLBL = 0;
    reg JTAG_SEL4_GLBL = 0;

    reg JTAG_USER_TDO1_GLBL = 1'bz;
    reg JTAG_USER_TDO2_GLBL = 1'bz;
    reg JTAG_USER_TDO3_GLBL = 1'bz;
    reg JTAG_USER_TDO4_GLBL = 1'bz;

    assign (strong1, weak0) GSR = GSR_int;
    assign (strong1, weak0) GTS = GTS_int;
    assign (weak1, weak0) PRLD = PRLD_int;
    assign (strong1, weak0) GRESTORE = GRESTORE_int;

    initial begin
	GSR_int = 1'b1;
	PRLD_int = 1'b1;
	#(ROC_WIDTH)
	GSR_int = 1'b0;
	PRLD_int = 1'b0;
    end

    initial begin
	GTS_int = 1'b1;
	#(TOC_WIDTH)
	GTS_int = 1'b0;
    end

    initial begin 
	GRESTORE_int = 1'b0;
	#(GRES_START);
	GRESTORE_int = 1'b1;
	#(GRES_WIDTH);
	GRESTORE_int = 1'b0;
    end

endmodule
`endif
