MichalVarsanyi/VoxLink/Firmware/Vivado/Projects/VoxLink_Controller/VoxLink_Controller.cache/ip/2024.1/a/6/a6a7915305ae47ab/blk_mem_gen_0_sim_netlist.vhdl

-- Copyright 1986-2022 Xilinx, Inc. All Rights Reserved.
-- Copyright 2022-2024 Advanced Micro Devices, Inc. All Rights Reserved.
-- --------------------------------------------------------------------------------
-- Tool Version: Vivado v.2024.1 (win64) Build 5076996 Wed May 22 18:37:14 MDT 2024
-- Date        : Tue May  5 16:36:00 2026
-- Host        : LAPTOP-GK6ER3TV running 64-bit major release  (build 9200)
-- Command     : write_vhdl -force -mode funcsim -rename_top decalper_eb_ot_sdeen_pot_pi_dehcac_xnilix -prefix
--               decalper_eb_ot_sdeen_pot_pi_dehcac_xnilix_ blk_mem_gen_0_sim_netlist.vhdl
-- Design      : blk_mem_gen_0
-- Purpose     : This VHDL netlist is a functional simulation representation of the design and should not be modified or
--               synthesized. This netlist cannot be used for SDF annotated simulation.
-- Device      : xc7a35tcsg324-1
-- --------------------------------------------------------------------------------
`protect begin_protected
`protect version = 1
`protect encrypt_agent = "XILINX"
`protect encrypt_agent_info = "Xilinx Encryption Tool 2024.1"
`protect key_keyowner="Synopsys", key_keyname="SNPS-VCS-RSA-2", key_method="rsa"
`protect encoding = (enctype="BASE64", line_length=76, bytes=128)
`protect key_block
RSqbsRZSIb+QlYJMfFv1T7uHQ7PiCEXQkl687MHGm2LgPB15GIYcPmqKUSXgtkLsIFes91PTAyyB
9H9cyY4ZUxedcRg/9ZOB5pm3zPqAbcvGPmg1ivMhr/MlS19t5lYKM2tQo+0Yd+arJXlVZu2BMnvn
+I3G9t9tJuWUIWKjI+I=

`protect key_keyowner="Aldec", key_keyname="ALDEC15_001", key_method="rsa"
`protect encoding = (enctype="BASE64", line_length=76, bytes=256)
`protect key_block
VRSQ05ZaB6bIhFIQ823mTvlJaG9+5iW5C3+KxGjq0sq9ziCshKOLpOGPDMmOWDqA4uBaxC5IKISr
w8+A8mqbYjXo5m1g8sGjNaETS0HKJsK+l5Y++tN4IEUs+DwxgrPR/+LWtChuOzVkfC7BG3LVUEMj
zM3GAyGcXGJ3sdBItZAfsevyiy7kr4Fw+nk2hWytGteu1NZk3VzPE7KQHLkOlHBPXf6P0j8LpKcr
2oNDgQ/WaEmg6OOvFeJuaWDaee8Sn6wKP/caMyoGdSeczsPtRrJeoSRlbNHlxhCv7zg+Cn2AgwrR
PTqGsMrkhv9U0sq+waS0CmwChsk4WB7RspGYUg==

`protect key_keyowner="Mentor Graphics Corporation", key_keyname="MGC-VELOCE-RSA", key_method="rsa"
`protect encoding = (enctype="BASE64", line_length=76, bytes=128)
`protect key_block
tNziOjCznlvIl4dadmB9r23Duf+HQHWOuHmupEU3PJxrazHVtZdNKspG9sRXhF9mjbpnSiKYCdFK
Jr9W/dxUid36faFIPKQazVTuOiE0hkzVQAGpYxXjT/ITB/9EFBvgvP5L3EAhHv32x6MA1vkFSI7x
HrZ09YNFEF6T7DPTZE4=

`protect key_keyowner="Mentor Graphics Corporation", key_keyname="MGC-VERIF-SIM-RSA-2", key_method="rsa"
`protect encoding = (enctype="BASE64", line_length=76, bytes=256)
`protect key_block
QCYfxgkUHlX1cre1q9aS3sVDIOX36YBK4ZwJXAVUwA6f1OQ77XibjpWJHt5FK9F0PcYp/j21pqzO
BRdkDcFLVAjxER4J5t5iMVhoeMk+3fpiKfYrm4WFl1ygsJsfFJP0jqO1OkjC8iFBtm3n6b7CTl1o
cjBbcBp8UgW6E8rf5inXA0dRqybnyxKJSnMFYLinvpVU6QEc4OKO7mi/i/s9p/efiP+CdQf0yDRU
Fw7o7x0D7tjBv943g5L+4wGZ2JYU+ISqn4Ajxy/bWTTJDe6T/15evhngS61MC8Xjamzc4YLZBP8o
ShfSLoeZeO+Hk5n3xzJRghM0DQ6Sj7NqXFY68w==

`protect key_keyowner="Real Intent", key_keyname="RI-RSA-KEY-1", key_method="rsa"
`protect encoding = (enctype="BASE64", line_length=76, bytes=256)
`protect key_block
Uy8FDDy3dZQGAnMQV0HBesEs+/oZdaq35Kj1PGhy9J/+EBZm0nhhQgYtku8tWABW2jKAC1GtNTvo
uReQyr1hteMxTbD5OIuqv86eb1hXZVENlZ7ichG8auUjkeHAkaSYNbHOuDLIhSqHEL67XbcZ9zPG
1JOY3+VONSww0KYPcQbGSo/2DaC5C0Y+mZODRfJ4+b0WXjce6UaJetilBc3VtqqmodIM2d3HDawF
R0xVJfHj86rXmUkY+SNUw60zsV6raCY6G3k/rXpei1d6zn8tCThkKG5fwiWY8zA7kRdTFIlVKP9h
fb6kfzRBRT/BgVQ8d4RgEcEVV8m3u/Mf4KIlTw==

`protect key_keyowner="Xilinx", key_keyname="xilinxt_2023_11", key_method="rsa"
`protect encoding = (enctype="BASE64", line_length=76, bytes=256)
`protect key_block
Pk1GeRlkUK9lt6DVXYVdtOABlzDEWQDcBsP/p+Wo5HaglDLG5b8gk08xTP3IcJ1RKcfuARPMGO2s
/VqFbnVADV90T1rhjIuWMcBnzYQK/ALUvwv11Uju9Gn0fvPIz52l3QBnpjHI1nlsFB7WeqkzVfHZ
tg9gO9bPHjHLjVd9BzH6McrEWY5RkZ0UBy0Fmh/SownJX1b0YGE7LdwKydEMEpyvb28bwTOwfEv/
4RtsfYtEvTjo6e1ZBm66D9IQmKUu32wzTfn5bFZHdyjZg6+HcTzvHMtQX2+AggXfP6FsO2/83qkb
0bfj226fnLhr32dJxtsaJS5OR63GYtzDJ05ITA==

`protect key_keyowner="Metrics Technologies Inc.", key_keyname="DSim", key_method="rsa"
`protect encoding = (enctype="BASE64", line_length=76, bytes=256)
`protect key_block
LCfWqKmUoUSVOTKNAl5p8n1hfz7SMU2kDOUMBjsDncgSFqiu2zUy1I6GSDrVnF/2umJG5/mWcpvi
rQaFJOlrJ8DNctSuavdlopRAwTMsVi6dAlNGrAawSiDIxtI3tN3MDVdMiH5H+pJMqMt59yXneyCf
2RRSRz2sUQK/aj0lXlqKjVJzVbk8HaBQ8akBJF4iWSMK4foIzJ6iO1EupYovuW6uEiO7jQRWezlW
pbbDenOHHWbfinuX5cbkjpTKHGsEKct65q+ZXJp60m3sconSK3Y2eLQxusuJ1FHDJ4GGKO8mEzCv
3cfGdXX3pVL81OfGO/JD1aMs9H98CO5ssbHqlw==

`protect key_keyowner="Atrenta", key_keyname="ATR-SG-RSA-1", key_method="rsa"
`protect encoding = (enctype="BASE64", line_length=76, bytes=384)
`protect key_block
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

`protect key_keyowner="Cadence Design Systems.", key_keyname="CDS_RSA_KEY_VER_1", key_method="rsa"
`protect encoding = (enctype="BASE64", line_length=76, bytes=256)
`protect key_block
gj+uMxV+tK4Di7pgSOE82FOBeWmUB1A7OKFOSMUW3qrmQ4/YhryfHMlWPxfAq8avQL7tnBTnRFEg
czbErdIcNzYjrM7Qq00QC/mTqmeQX4/apbqGvN+rwK4RR5oj22wfTib/UQNEQX6fbpi6PtmAeUR9
eShsfq+YWcf7z2Zw4Q+o4+E6m4/3CzU68vglNpzNsJ8S9/8XpdIrvAA/WRAX6OEOC4wlNIKDZsq/
+zMbFgSzN1rP844I/CDmxYM0NIzBWWhYBkPfJyQyigmUoXb84lDip0/Dmnq4EHvu7D/tZNnDl5st
JpftRfEpT6S8e/5MBeKUuhbfg6etHo/oFZvPKQ==

`protect key_keyowner="Synplicity", key_keyname="SYNP15_1", key_method="rsa"
`protect encoding = (enctype="BASE64", line_length=76, bytes=256)
`protect key_block
aWTy3xv6SqKsldtLS2gY4KrTS8U+KtFNRHS314f6EYZy1MHE9t7oICJ8eNB8up8A+odoE23N3fJb
1alhaadeRWU2GjlIiK1LjZ5PQw+jb1u1GWtRiY+TcTlD75XUlqwykVBrCDfm565DmgZjZle9T3/t
WEfLo+m/8GfBe8trVnoftsk/XI00BMFXRzw8doPGDhNECS1NUrLebryb9iO5Hf4A/40dtslTARsR
nicN0KoIIyiQ+QzliqyXU/8VjS45inON8R0Kv9Qx46EXUp7bds5uQ7QycRhpLG0IPnMIweudU67w
eQmpHJzvZKBCZks/R0OafZx44H6Jib2+QazBCw==

`protect key_keyowner="Mentor Graphics Corporation", key_keyname="MGC-PREC-RSA", key_method="rsa"
`protect encoding = (enctype="BASE64", line_length=76, bytes=256)
`protect key_block
UGdPiChIPj1lSozqzCQx17Bi+8FWSuMUMzXUkDLH5zcP1t8tZLzh4CU4WAR8lmJxn8gH763fLp5c
RYU6zA0yxHzl2ksc5YRU1XEfQQT9ha8fQnz+18wVKcsa5UIOfMbGDwnS9yfX59ntG8CB0uF8bJKE
y1CS6U/1Stfs1w2mF94iDxI2n2GJlb1UPtWpmxMBI88hY0GktTPXP2Y7JKl8zRl/Lq0wIF8pHwXk
B4nOgKm6hfzPj0xZ6E/TuER/JE3fy8RSm24IlL/CUgpReEslEOYjQ4EKKZRG9/fxg26utQWW9p+G
fWVU53qrFGzBhKQ96Paj1ROkv6hDHyUb6n7uSw==

`protect data_method = "AES128-CBC"
`protect encoding = (enctype = "BASE64", line_length = 76, bytes = 68304)
`protect data_block
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
Y3vFyRkhVmAxR4nWYHOuaoCn
`protect end_protected
library IEEE;
use IEEE.STD_LOGIC_1164.ALL;
library UNISIM;
use UNISIM.VCOMPONENTS.ALL;
entity decalper_eb_ot_sdeen_pot_pi_dehcac_xnilix is
  port (
    clka : in STD_LOGIC;
    ena : in STD_LOGIC;
    wea : in STD_LOGIC_VECTOR ( 0 to 0 );
    addra : in STD_LOGIC_VECTOR ( 6 downto 0 );
    dina : in STD_LOGIC_VECTOR ( 111 downto 0 );
    douta : out STD_LOGIC_VECTOR ( 111 downto 0 )
  );
  attribute NotValidForBitStream : boolean;
  attribute NotValidForBitStream of decalper_eb_ot_sdeen_pot_pi_dehcac_xnilix : entity is true;
  attribute CHECK_LICENSE_TYPE : string;
  attribute CHECK_LICENSE_TYPE of decalper_eb_ot_sdeen_pot_pi_dehcac_xnilix : entity is "blk_mem_gen_0,blk_mem_gen_v8_4_8,{}";
  attribute downgradeipidentifiedwarnings : string;
  attribute downgradeipidentifiedwarnings of decalper_eb_ot_sdeen_pot_pi_dehcac_xnilix : entity is "yes";
  attribute x_core_info : string;
  attribute x_core_info of decalper_eb_ot_sdeen_pot_pi_dehcac_xnilix : entity is "blk_mem_gen_v8_4_8,Vivado 2024.1";
end decalper_eb_ot_sdeen_pot_pi_dehcac_xnilix;

architecture STRUCTURE of decalper_eb_ot_sdeen_pot_pi_dehcac_xnilix is
  signal NLW_U0_dbiterr_UNCONNECTED : STD_LOGIC;
  signal NLW_U0_rsta_busy_UNCONNECTED : STD_LOGIC;
  signal NLW_U0_rstb_busy_UNCONNECTED : STD_LOGIC;
  signal NLW_U0_s_axi_arready_UNCONNECTED : STD_LOGIC;
  signal NLW_U0_s_axi_awready_UNCONNECTED : STD_LOGIC;
  signal NLW_U0_s_axi_bvalid_UNCONNECTED : STD_LOGIC;
  signal NLW_U0_s_axi_dbiterr_UNCONNECTED : STD_LOGIC;
  signal NLW_U0_s_axi_rlast_UNCONNECTED : STD_LOGIC;
  signal NLW_U0_s_axi_rvalid_UNCONNECTED : STD_LOGIC;
  signal NLW_U0_s_axi_sbiterr_UNCONNECTED : STD_LOGIC;
  signal NLW_U0_s_axi_wready_UNCONNECTED : STD_LOGIC;
  signal NLW_U0_sbiterr_UNCONNECTED : STD_LOGIC;
  signal NLW_U0_doutb_UNCONNECTED : STD_LOGIC_VECTOR ( 111 downto 0 );
  signal NLW_U0_rdaddrecc_UNCONNECTED : STD_LOGIC_VECTOR ( 6 downto 0 );
  signal NLW_U0_s_axi_bid_UNCONNECTED : STD_LOGIC_VECTOR ( 3 downto 0 );
  signal NLW_U0_s_axi_bresp_UNCONNECTED : STD_LOGIC_VECTOR ( 1 downto 0 );
  signal NLW_U0_s_axi_rdaddrecc_UNCONNECTED : STD_LOGIC_VECTOR ( 6 downto 0 );
  signal NLW_U0_s_axi_rdata_UNCONNECTED : STD_LOGIC_VECTOR ( 111 downto 0 );
  signal NLW_U0_s_axi_rid_UNCONNECTED : STD_LOGIC_VECTOR ( 3 downto 0 );
  signal NLW_U0_s_axi_rresp_UNCONNECTED : STD_LOGIC_VECTOR ( 1 downto 0 );
  attribute C_ADDRA_WIDTH : integer;
  attribute C_ADDRA_WIDTH of U0 : label is 7;
  attribute C_ADDRB_WIDTH : integer;
  attribute C_ADDRB_WIDTH of U0 : label is 7;
  attribute C_ALGORITHM : integer;
  attribute C_ALGORITHM of U0 : label is 1;
  attribute C_AXI_ID_WIDTH : integer;
  attribute C_AXI_ID_WIDTH of U0 : label is 4;
  attribute C_AXI_SLAVE_TYPE : integer;
  attribute C_AXI_SLAVE_TYPE of U0 : label is 0;
  attribute C_AXI_TYPE : integer;
  attribute C_AXI_TYPE of U0 : label is 1;
  attribute C_BYTE_SIZE : integer;
  attribute C_BYTE_SIZE of U0 : label is 9;
  attribute C_COMMON_CLK : integer;
  attribute C_COMMON_CLK of U0 : label is 0;
  attribute C_COUNT_18K_BRAM : string;
  attribute C_COUNT_18K_BRAM of U0 : label is "0";
  attribute C_COUNT_36K_BRAM : string;
  attribute C_COUNT_36K_BRAM of U0 : label is "2";
  attribute C_CTRL_ECC_ALGO : string;
  attribute C_CTRL_ECC_ALGO of U0 : label is "NONE";
  attribute C_DEFAULT_DATA : string;
  attribute C_DEFAULT_DATA of U0 : label is "0";
  attribute C_DISABLE_WARN_BHV_COLL : integer;
  attribute C_DISABLE_WARN_BHV_COLL of U0 : label is 0;
  attribute C_DISABLE_WARN_BHV_RANGE : integer;
  attribute C_DISABLE_WARN_BHV_RANGE of U0 : label is 0;
  attribute C_ELABORATION_DIR : string;
  attribute C_ELABORATION_DIR of U0 : label is "./";
  attribute C_ENABLE_32BIT_ADDRESS : integer;
  attribute C_ENABLE_32BIT_ADDRESS of U0 : label is 0;
  attribute C_EN_DEEPSLEEP_PIN : integer;
  attribute C_EN_DEEPSLEEP_PIN of U0 : label is 0;
  attribute C_EN_ECC_PIPE : integer;
  attribute C_EN_ECC_PIPE of U0 : label is 0;
  attribute C_EN_RDADDRA_CHG : integer;
  attribute C_EN_RDADDRA_CHG of U0 : label is 0;
  attribute C_EN_RDADDRB_CHG : integer;
  attribute C_EN_RDADDRB_CHG of U0 : label is 0;
  attribute C_EN_SAFETY_CKT : integer;
  attribute C_EN_SAFETY_CKT of U0 : label is 0;
  attribute C_EN_SHUTDOWN_PIN : integer;
  attribute C_EN_SHUTDOWN_PIN of U0 : label is 0;
  attribute C_EN_SLEEP_PIN : integer;
  attribute C_EN_SLEEP_PIN of U0 : label is 0;
  attribute C_EST_POWER_SUMMARY : string;
  attribute C_EST_POWER_SUMMARY of U0 : label is "Estimated Power for IP     :     12.8379 mW";
  attribute C_FAMILY : string;
  attribute C_FAMILY of U0 : label is "artix7";
  attribute C_HAS_AXI_ID : integer;
  attribute C_HAS_AXI_ID of U0 : label is 0;
  attribute C_HAS_ENA : integer;
  attribute C_HAS_ENA of U0 : label is 1;
  attribute C_HAS_ENB : integer;
  attribute C_HAS_ENB of U0 : label is 0;
  attribute C_HAS_INJECTERR : integer;
  attribute C_HAS_INJECTERR of U0 : label is 0;
  attribute C_HAS_MEM_OUTPUT_REGS_A : integer;
  attribute C_HAS_MEM_OUTPUT_REGS_A of U0 : label is 1;
  attribute C_HAS_MEM_OUTPUT_REGS_B : integer;
  attribute C_HAS_MEM_OUTPUT_REGS_B of U0 : label is 0;
  attribute C_HAS_MUX_OUTPUT_REGS_A : integer;
  attribute C_HAS_MUX_OUTPUT_REGS_A of U0 : label is 0;
  attribute C_HAS_MUX_OUTPUT_REGS_B : integer;
  attribute C_HAS_MUX_OUTPUT_REGS_B of U0 : label is 0;
  attribute C_HAS_REGCEA : integer;
  attribute C_HAS_REGCEA of U0 : label is 0;
  attribute C_HAS_REGCEB : integer;
  attribute C_HAS_REGCEB of U0 : label is 0;
  attribute C_HAS_RSTA : integer;
  attribute C_HAS_RSTA of U0 : label is 0;
  attribute C_HAS_RSTB : integer;
  attribute C_HAS_RSTB of U0 : label is 0;
  attribute C_HAS_SOFTECC_INPUT_REGS_A : integer;
  attribute C_HAS_SOFTECC_INPUT_REGS_A of U0 : label is 0;
  attribute C_HAS_SOFTECC_OUTPUT_REGS_B : integer;
  attribute C_HAS_SOFTECC_OUTPUT_REGS_B of U0 : label is 0;
  attribute C_INITA_VAL : string;
  attribute C_INITA_VAL of U0 : label is "0";
  attribute C_INITB_VAL : string;
  attribute C_INITB_VAL of U0 : label is "0";
  attribute C_INIT_FILE : string;
  attribute C_INIT_FILE of U0 : label is "blk_mem_gen_0.mem";
  attribute C_INIT_FILE_NAME : string;
  attribute C_INIT_FILE_NAME of U0 : label is "no_coe_file_loaded";
  attribute C_INTERFACE_TYPE : integer;
  attribute C_INTERFACE_TYPE of U0 : label is 0;
  attribute C_LOAD_INIT_FILE : integer;
  attribute C_LOAD_INIT_FILE of U0 : label is 0;
  attribute C_MEM_TYPE : integer;
  attribute C_MEM_TYPE of U0 : label is 0;
  attribute C_MUX_PIPELINE_STAGES : integer;
  attribute C_MUX_PIPELINE_STAGES of U0 : label is 0;
  attribute C_PRIM_TYPE : integer;
  attribute C_PRIM_TYPE of U0 : label is 1;
  attribute C_READ_DEPTH_A : integer;
  attribute C_READ_DEPTH_A of U0 : label is 128;
  attribute C_READ_DEPTH_B : integer;
  attribute C_READ_DEPTH_B of U0 : label is 128;
  attribute C_READ_LATENCY_A : integer;
  attribute C_READ_LATENCY_A of U0 : label is 1;
  attribute C_READ_LATENCY_B : integer;
  attribute C_READ_LATENCY_B of U0 : label is 1;
  attribute C_READ_WIDTH_A : integer;
  attribute C_READ_WIDTH_A of U0 : label is 112;
  attribute C_READ_WIDTH_B : integer;
  attribute C_READ_WIDTH_B of U0 : label is 112;
  attribute C_RSTRAM_A : integer;
  attribute C_RSTRAM_A of U0 : label is 0;
  attribute C_RSTRAM_B : integer;
  attribute C_RSTRAM_B of U0 : label is 0;
  attribute C_RST_PRIORITY_A : string;
  attribute C_RST_PRIORITY_A of U0 : label is "CE";
  attribute C_RST_PRIORITY_B : string;
  attribute C_RST_PRIORITY_B of U0 : label is "CE";
  attribute C_SIM_COLLISION_CHECK : string;
  attribute C_SIM_COLLISION_CHECK of U0 : label is "ALL";
  attribute C_USE_BRAM_BLOCK : integer;
  attribute C_USE_BRAM_BLOCK of U0 : label is 0;
  attribute C_USE_BYTE_WEA : integer;
  attribute C_USE_BYTE_WEA of U0 : label is 0;
  attribute C_USE_BYTE_WEB : integer;
  attribute C_USE_BYTE_WEB of U0 : label is 0;
  attribute C_USE_DEFAULT_DATA : integer;
  attribute C_USE_DEFAULT_DATA of U0 : label is 0;
  attribute C_USE_ECC : integer;
  attribute C_USE_ECC of U0 : label is 0;
  attribute C_USE_SOFTECC : integer;
  attribute C_USE_SOFTECC of U0 : label is 0;
  attribute C_USE_URAM : integer;
  attribute C_USE_URAM of U0 : label is 0;
  attribute C_WEA_WIDTH : integer;
  attribute C_WEA_WIDTH of U0 : label is 1;
  attribute C_WEB_WIDTH : integer;
  attribute C_WEB_WIDTH of U0 : label is 1;
  attribute C_WRITE_DEPTH_A : integer;
  attribute C_WRITE_DEPTH_A of U0 : label is 128;
  attribute C_WRITE_DEPTH_B : integer;
  attribute C_WRITE_DEPTH_B of U0 : label is 128;
  attribute C_WRITE_MODE_A : string;
  attribute C_WRITE_MODE_A of U0 : label is "WRITE_FIRST";
  attribute C_WRITE_MODE_B : string;
  attribute C_WRITE_MODE_B of U0 : label is "WRITE_FIRST";
  attribute C_WRITE_WIDTH_A : integer;
  attribute C_WRITE_WIDTH_A of U0 : label is 112;
  attribute C_WRITE_WIDTH_B : integer;
  attribute C_WRITE_WIDTH_B of U0 : label is 112;
  attribute C_XDEVICEFAMILY : string;
  attribute C_XDEVICEFAMILY of U0 : label is "artix7";
  attribute downgradeipidentifiedwarnings of U0 : label is "yes";
  attribute is_du_within_envelope : string;
  attribute is_du_within_envelope of U0 : label is "true";
  attribute x_interface_info : string;
  attribute x_interface_info of clka : signal is "xilinx.com:interface:bram:1.0 BRAM_PORTA CLK";
  attribute x_interface_parameter : string;
  attribute x_interface_parameter of clka : signal is "XIL_INTERFACENAME BRAM_PORTA, MEM_ADDRESS_MODE BYTE_ADDRESS, MEM_SIZE 8192, MEM_WIDTH 32, MEM_ECC NONE, MASTER_TYPE OTHER, READ_LATENCY 1";
  attribute x_interface_info of ena : signal is "xilinx.com:interface:bram:1.0 BRAM_PORTA EN";
  attribute x_interface_info of addra : signal is "xilinx.com:interface:bram:1.0 BRAM_PORTA ADDR";
  attribute x_interface_info of dina : signal is "xilinx.com:interface:bram:1.0 BRAM_PORTA DIN";
  attribute x_interface_info of douta : signal is "xilinx.com:interface:bram:1.0 BRAM_PORTA DOUT";
  attribute x_interface_info of wea : signal is "xilinx.com:interface:bram:1.0 BRAM_PORTA WE";
begin
U0: entity work.decalper_eb_ot_sdeen_pot_pi_dehcac_xnilix_blk_mem_gen_v8_4_8
     port map (
      addra(6 downto 0) => addra(6 downto 0),
      addrb(6 downto 0) => B"0000000",
      clka => clka,
      clkb => '0',
      dbiterr => NLW_U0_dbiterr_UNCONNECTED,
      deepsleep => '0',
      dina(111 downto 0) => dina(111 downto 0),
      dinb(111 downto 0) => B"0000000000000000000000000000000000000000000000000000000000000000000000000000000000000000000000000000000000000000",
      douta(111 downto 0) => douta(111 downto 0),
      doutb(111 downto 0) => NLW_U0_doutb_UNCONNECTED(111 downto 0),
      eccpipece => '0',
      ena => ena,
      enb => '0',
      injectdbiterr => '0',
      injectsbiterr => '0',
      rdaddrecc(6 downto 0) => NLW_U0_rdaddrecc_UNCONNECTED(6 downto 0),
      regcea => '1',
      regceb => '1',
      rsta => '0',
      rsta_busy => NLW_U0_rsta_busy_UNCONNECTED,
      rstb => '0',
      rstb_busy => NLW_U0_rstb_busy_UNCONNECTED,
      s_aclk => '0',
      s_aresetn => '0',
      s_axi_araddr(31 downto 0) => B"00000000000000000000000000000000",
      s_axi_arburst(1 downto 0) => B"00",
      s_axi_arid(3 downto 0) => B"0000",
      s_axi_arlen(7 downto 0) => B"00000000",
      s_axi_arready => NLW_U0_s_axi_arready_UNCONNECTED,
      s_axi_arsize(2 downto 0) => B"000",
      s_axi_arvalid => '0',
      s_axi_awaddr(31 downto 0) => B"00000000000000000000000000000000",
      s_axi_awburst(1 downto 0) => B"00",
      s_axi_awid(3 downto 0) => B"0000",
      s_axi_awlen(7 downto 0) => B"00000000",
      s_axi_awready => NLW_U0_s_axi_awready_UNCONNECTED,
      s_axi_awsize(2 downto 0) => B"000",
      s_axi_awvalid => '0',
      s_axi_bid(3 downto 0) => NLW_U0_s_axi_bid_UNCONNECTED(3 downto 0),
      s_axi_bready => '0',
      s_axi_bresp(1 downto 0) => NLW_U0_s_axi_bresp_UNCONNECTED(1 downto 0),
      s_axi_bvalid => NLW_U0_s_axi_bvalid_UNCONNECTED,
      s_axi_dbiterr => NLW_U0_s_axi_dbiterr_UNCONNECTED,
      s_axi_injectdbiterr => '0',
      s_axi_injectsbiterr => '0',
      s_axi_rdaddrecc(6 downto 0) => NLW_U0_s_axi_rdaddrecc_UNCONNECTED(6 downto 0),
      s_axi_rdata(111 downto 0) => NLW_U0_s_axi_rdata_UNCONNECTED(111 downto 0),
      s_axi_rid(3 downto 0) => NLW_U0_s_axi_rid_UNCONNECTED(3 downto 0),
      s_axi_rlast => NLW_U0_s_axi_rlast_UNCONNECTED,
      s_axi_rready => '0',
      s_axi_rresp(1 downto 0) => NLW_U0_s_axi_rresp_UNCONNECTED(1 downto 0),
      s_axi_rvalid => NLW_U0_s_axi_rvalid_UNCONNECTED,
      s_axi_sbiterr => NLW_U0_s_axi_sbiterr_UNCONNECTED,
      s_axi_wdata(111 downto 0) => B"0000000000000000000000000000000000000000000000000000000000000000000000000000000000000000000000000000000000000000",
      s_axi_wlast => '0',
      s_axi_wready => NLW_U0_s_axi_wready_UNCONNECTED,
      s_axi_wstrb(0) => '0',
      s_axi_wvalid => '0',
      sbiterr => NLW_U0_sbiterr_UNCONNECTED,
      shutdown => '0',
      sleep => '0',
      wea(0) => wea(0),
      web(0) => '0'
    );
end STRUCTURE;
